jdg511/GAS/hardware/kicad/rev-a-capture-audit.md

# GAS Rev A Capture Audit

Generated by `python hardware/kicad/audit-rev-a-capture.py --output C:/Users/Jason/GAS-build/repo/hardware/kicad/rev-a-capture-audit.md`.

## Top-Level Hierarchy

- Hierarchical child sheets present: `6` / `6`
- Missing sheet files: none

## Symbol Population

| Sheet | Refs Found | Completion | Optional Refs Found |
| --- | ---: | ---: | ---: |
| io-board | 14/14 | 100.0% | 0 |
| tank-driver-recovery | 19/19 | 100.0% | 0 |
| ext-tank-routing | 12/12 | 100.0% | 0 |
| crossfade-feedback-wet | 8/8 | 100.0% | 0 |
| filter-clipper | 19/19 | 100.0% | 0 |
| power-backplane | 16/16 | 100.0% | 0 |

## Missing References By Sheet

### io-board

- Missing required refs: none

### tank-driver-recovery

- Missing required refs: none

### ext-tank-routing

- Missing required refs: none

### crossfade-feedback-wet

- Missing required refs: none

### filter-clipper

- Missing required refs: none

### power-backplane

- Missing required refs: none
- Optional refs still absent: `U601`

## Net Label Coverage

| Scope | Labels Found | Completion |
| --- | ---: | ---: |
| global | 5/5 | 100.0% |
| io-boundary | 8/8 | 100.0% |
| inter-board | 22/22 | 100.0% |
| control | 47/47 | 100.0% |

## Missing Net Labels

### global

- Missing labels: none

### io-boundary

- Missing labels: none

### inter-board

- Missing labels: none

### control

- Missing labels: none

## Notes

- This audit intentionally measures only what is visible in the checked-in schematic text: sheet files, symbol reference designators, and explicit labels.
- It does not claim analog correctness, ERC cleanliness, or footprint completeness.
- A placeholder child sheet will therefore score `0%` until real symbols and labels are entered.
