jdg511/GAS/hardware/kicad/datasheet_cache/g5v2.summary.md

# Omron G5V-2 (DPDT signal relay) — datasheet summary
Status: partially verified (contact ratings from text; coil table is a
graphic — needs-human-check at order time)
- Contacts: rated 0.5 A/125 VAC, 2 A/30 VDC; carry 2 A. Audio/logic signals
  here are mA-level: PASS with large margin.
- Coils used: DC5 (K201-K204, K401-K403; ~30-40 mA each assumed) and DC12
  (K301, fed from +15VA through R351 240R sized for a ~960R coil).
  ACTION AT ORDER: confirm coil resistance of the exact DC5/DC12 variants;
  if DC12 coil is 720R, R351 -> 150R.
- Pinout used: 1/16 coil; 4 COM1, 6 NC1, 8 NO1; 13 COM2, 11 NC2, 9 NO2
  (KiCad library symbol geometry). NC/NO polarity affects which panel
  position means 'inverted'/mode — bench-verify once, swap wires if flipped.
