jdg511/GAS/hardware/kicad/datasheet_cache/jst-vh.summary.md

# JST VH connector family — datasheet summary
Status: verified (rating block read visually, datasheet_cache/eVH_35d0fc229b.pdf p.1)
- 10 A (AWG#16) / 7 A (AWG#18), 250 V. Rails carry <=0.25 A/pin: <4%: PASS.
