jdg511/GAS/hardware/kicad/datasheet_cache/jst-xh.summary.md

# JST XH connector family — datasheet summary
Status: verified (rating block read visually, datasheet_cache/eXH_98b6fe789a.pdf p.1)
- 3 A AC/DC (AWG#22), 250 V, contact R 10 mOhm initial, wire 30-22 AWG.
- Worst path on XH here: +30 V DC input landing P500 ~0.36 A = 12%: PASS.
  Tank sends ~65 mA pk, audio signals lower: PASS.
