jdg511/GAS/hardware/kicad/datasheet_cache/opa1644.summary.md

# OPA1644 (SOIC-14 quad JFET audio op amp) — datasheet summary
Status: verified for supply range (cached PDF datasheet_cache/opa1644_652e77ac8c.pdf)
- Supply: +/-2.25 V to +/-18 V. +/-15 V used: PASS. JFET input, pA bias.
- KiCad symbol used: TL074 (identical industry quad pinout as above).
