jdg511/GAS/hardware/kicad/datasheet_cache/opa1656.summary.md

# OPA1656 (SOIC-8 dual audio op amp) — datasheet summary
Status: verified (pin table, ROC, cached PDF datasheet_cache/opa1656_eb3ddbf012.pdf)
## Key limits (datasheet text evidence)
- Supply: +/-2.25 V to +/-18 V (4.5-36 V). Design uses +/-15 V: PASS.
- Output current: 100 mA; short-circuit +/-100 mA.
- Iq ~3.9 mA/ch (~7.8 mA/package).
## Pin-level requirements (SOIC-8 dual)
1 OUT_A | 2 IN_A- | 3 IN_A+ | 4 V- | 5 IN_B+ | 6 IN_B- | 7 OUT_B | 8 V+
- V+/V- require local decoupling (100 nF class) per rail.
- CMOS inputs: pA bias; high-value bias resistors (2.2M) acceptable.
