jdg511/GAS/hardware/kicad/datasheet_cache/opa1679.summary.md

# OPA1679 (SOIC-14 quad audio op amp) — datasheet summary
Status: verified (supply range from cached PDF datasheet_cache/opa1679_e09979f1c7.pdf)
- Supply: +/-2.25 V to +/-18 V (4.5-36 V), ~2 mA/ch. +/-15 V used: PASS.
- Output-drive spec not text-extracted: loads in this design are >=10k or
  behind 100-220R isolators (<5 mA) — needs-human-check only for margins.
## Pins (standard quad): 1 OUT_A, 2 IN_A-, 3 IN_A+, 4 V+, 5 IN_B+, 6 IN_B-,
7 OUT_B, 8 OUT_C, 9 IN_C-, 10 IN_C+, 11 V-, 12 IN_D+, 13 IN_D-, 14 OUT_D.
