jdg511/GAS/hardware/kicad/datasheet_cache/r78e.summary.md

# RECOM R-78E5.0-0.5 — datasheet summary
Status: verified (text, datasheet_cache/R-78E-0.5_4908d77dcc.pdf)
- Input 7-28 VDC, output 5 V 0.5 A, 7805 pinout (1 Vin, 2 GND, 3 Vout).
- Fed from +15VRAW (review fix F1): inside range, PASS. Load worst-case
  ~210 mA (relay coils): 42% of rating, PASS.
- Externals: input cap C512 10u (added), output C507 47u + C508 100n: PASS.
