jdg511/GAS/hardware/kicad/review_outputs/filt-U401-U402.md

# Instance review: U401/U402 (OPA1679 x2, filter-clipper)
Datasheet summary: datasheet_cache/opa1679.summary.md

| Pin/Group | Net | Check | Result |
| --- | --- | --- | --- |
| U401 A/B | HPF buffers (47n + pot rheostat) | fc 33 Hz-3.4 kHz | pass (sim) |
| U401 C/D | drive 4.9x fixed | sim exact | pass |
| U402 A/B | LPF buffers (pot series + 10n) | fc 157 Hz-16 kHz | pass (sim) |
| U402 C/D | output buffers + 100R isolators |  | pass |
| power units | +/-15 V + 100n x4 + 22u x2 |  | pass |

## Required externals
Audio-path caps are film-footprint (1210 ECHU class): policy pass.

## Findings
None.

Evidence: extracted JSON (rebuild/review-extract-filter-clipper.json), raw .kicad_sch
spot-check, datasheet summary above, verified ngspice run. Confidence: high
unless noted.
