jdg511/GAS/hardware/kicad/review_outputs/tdr-Q101-Q104.md

# Instance review: Q101-Q104 (BD139-16/BD140-16, tank-driver-recovery)
Datasheet summary: datasheet_cache/bd139-bd140.summary.md

| Pin/Group | Net | Check | Result |
| --- | --- | --- | --- |
| B/C/E | base stoppers 68R; C to rails; 0.33R emitters to PRI_OUT | class-B in-loop | pass (sim) |
| bias reserve | D101/D102/D121/D122 DNP | spec-frozen reserve | pass |

## Required externals
Datasheet not cached: dissipation margin is schematic+sim consistency only.

## Findings
manual_review: verify SOA/hFE bin from ST datasheet before production.

Evidence: extracted JSON (rebuild/review-extract-tank-driver-recovery.json), raw .kicad_sch
spot-check, datasheet summary above, verified ngspice run. Confidence: high
unless noted.
