jdg511/GAS/hardware/kicad/review_outputs/tdr-U102-U104.md

# Instance review: U102-U104 (OPA1656 x3, tank-driver-recovery)
Datasheet summary: datasheet_cache/opa1656.summary.md

| Pin/Group | Net | Check | Result |
| --- | --- | --- | --- |
| U102 A/B | SEC sends, gain 2.2 into 800R tanks | sim: 1.04 Vpk out | pass |
| U103/U104 A/B | recovery, gain 34, 2.2M bias to AGND | CMOS pA bias: OK | pass |
| power units | +15VA/-15VA + 100n each | decoupling present | pass |

## Required externals
Recovery offset x34 -> ~17 mV DC downstream (bench note, see final report).

## Findings
None.

Evidence: extracted JSON (rebuild/review-extract-tank-driver-recovery.json), raw .kicad_sch
spot-check, datasheet summary above, verified ngspice run. Confidence: high
unless noted.
