jdg511/GAS/hardware/bom/rev-a-input-output-priced-bom.csv

Board | RefDes | Qty | Manufacturer | MPN | Description | UnitPrice | Currency | Supplier | ExtPrice | BuyURL | AssemblyScope | Notes
Input/Output | U1 | 1 | Texas Instruments | OPA1644AIDR | Quad JFET-input audio op amp | 4.65 | USD | DigiKey | 4.65 | https://www.digikey.com/en/products/detail/texas-instruments/OPA1644AIDR/2353575 | SMD | Balanced receiver and mono-routing utility; current DigiKey page still shows the part as not normally stocked
Input/Output | U2-U4 | 3 | Texas Instruments | OPA1656IDR | Dual audio op amp | 2.99 | USD | DigiKey | 8.97 | https://www.digikey.com/en/products/detail/texas-instruments/OPA1656IDR/10715414 | SMD | Wet/dry mix plus fully active balanced output stages
Input/Output | J1-J4 | 4 | Neutrik | NCJ6FI-S | Combo XLR female / 1/4 TRS chassis receptacle | 4.71 | USD | Mouser | 18.84 | https://www.mouser.com/ProductDetail/Neutrik/NCJ6FI-S?qs=2AuUxvzm3x9XIIQSbwRdvA%3D%3D | Panel-DNP | Panel part; usually excluded from SMT quote
Input/Output | P1 | 1 | JST Sales America Inc. | B3P-VH-B | 3-position 3.96mm through-hole header | 0.23 | USD | DigiKey | 0.23 | https://www.digikey.com/en/products/detail/jst-sales-america-inc/B3P-VH-B/9924220 | TH | Board power input
Input/Output | P2-P4,P6 (+ P5 family placeholder) | 5 | JST Sales America Inc. | B3B-XH-A | 2.50mm JST XH-family header pricing placeholder | 0.15 | USD | DigiKey | 0.75 | https://www.digikey.com/en/products/detail/jst-sales-america-inc/B3B-XH-A/1651046 | TH | Priced as the common XH-family baseline only; `P5` is actually a larger 6-wire wet/dry landing and must be finalized as the matching higher-position XH-family part during the real PCB release
