jdg511/GAS/hardware/bom/rev-a-panel-and-mechanical-reference-bom.csv

Category | Subsystem | Qty | Manufacturer | MPN | Description | UnitPrice | Currency | Supplier | ExtPrice | BuyURL | Notes
Combo Jack | External I/O | 4 | Neutrik | NCJ6FI-S | Combo XLR female / 1/4 TRS chassis receptacle, solder cup | 4.71 | USD | Mouser | 18.84 | https://www.mouser.com/ProductDetail/Neutrik/NCJ6FI-S?qs=2AuUxvzm3x9XIIQSbwRdvA%3D%3D | Current reference combo-jack family for the fixed XLR/TRS requirement
Combo Jack Alt | External I/O | 4 | Neutrik | NCJ6FA-H | Combo XLR female / 1/4 TRS chassis receptacle, horizontal PCB mount | 0 | USD | Neutrik | 0 | https://www.neutrik.com/en/product/ncj6fa-h | Alternative if the enclosure and PCB benefit from direct combo-jack PCB mounting
DC Jack | Chassis Power | 1 | Same Sky | PJ-005A | Panel-mount DC barrel jack, 5.5 mm OD / 2.1 mm ID, center positive | 3.07 | USD | DigiKey | 3.07 | https://www.digikey.com/en/products/detail/same-sky-formerly-cui-devices/PJ-005A/165838 | Matches the Triad WSU240-0750 wall-adapter barrel size; same mounting hole as PJ-005B
Round Endcap Blank | Mechanical | 1 | Online Metals | AL-6061-PLATE-10IN-0125 | Reference 6061 aluminum plate blank for circular service endcap, 10 in x 0.125 in | 0 | USD | OnlineMetals | 0 | https://www.onlinemetals.com/en/buy/aluminum/0-125-aluminum-plate-6061-t6/pid/21631 | Size changed 9 in -> 10 in with diameter decision; price and exact SKU need requote at 10 in
Reinforcement Plate | Mechanical | 1 | Online Metals | AL-5052-PLATE-7IN-0090 | Reference aluminum reinforcement plate for jack bar and control support | 8.65 | USD | OnlineMetals | 8.65 | https://www.onlinemetals.com/en/buy/aluminum/0-09-aluminum-sheet-5052-h32/pid/11292 | Reference raw stock for the internal jack bar or local stiffener
Standoff Kit | Mechanical | 1 | Keystone | 2203 | Aluminum hex standoff assortment reference, 4-40 thread | 6.20 | USD | DigiKey | 6.20 | https://www.digikey.com/en/products/detail/keystone-electronics/2203/316133 | Reference internal rail or board-mount hardware
