jdg511/GAS/hardware/bom/rev-a-power-backplane-priced-bom.csv

Board | RefDes | Qty | Manufacturer | MPN | Description | UnitPrice | Currency | Supplier | ExtPrice | BuyURL | AssemblyScope | Notes
Power Backplane | J500 | 1 | Same Sky | PJ-005A | Panel-mount DC barrel jack, 5.5 mm OD / 2.1 mm ID, center positive | 3.07 | USD | DigiKey | 3.07 | https://www.digikey.com/en/products/detail/same-sky-formerly-cui-devices/PJ-005A/165838 | Panel-DNP | Service-endcap DC input jack; matches Triad WSU240-0750 2.1mm plug; same mounting hole/hardware as prior PJ-005B
Power Backplane | EXT-PSU | 1 | Triad Magnetics | WSU240-0750 | External wall adapter, +24VDC 750mA 18W regulated SMPS, UL 62368-1, 5.5x2.1mm center-positive plug | 12.43 | USD | DigiKey | 12.43 | https://www.digikey.com/en/products/detail/triad-magnetics/WSU240-0750/3094933 | External | Selected 2026-07-04; supersedes Jameco DDU300050E9340 candidate; alternates: Tri-Mag L6R20-240, Triad WSU240-1000
Power Backplane | PS500 | 1 | Mornsun | URA2415YMD-10WR3 | Isolated DC-DC module, 9-36V in (24V nominal), +/-15V dual at 10W out | 9.27 | USD | DigiKey | 9.27 | https://www.digikey.com/en/products/detail/mornsun-america-llc/URA2415YMD-10WR3/13160913 | SMD-or-module | Primary +/-15V generation
Power Backplane | PS501 | 1 | RECOM | R-78E5.0-0.5 | Switching regulator module, +5V/500mA out | 3.37 | USD | DigiKey | 3.37 | https://www.digikey.com/en/products/detail/recom-power/R-78E5-0-0-5/2834904 | SMD-or-module | +5VAUX generation
Power Backplane | P501-P505 | 5 | JST Sales America Inc. | B3P-VH-B | 3-position 3.96mm through-hole header | 0.23 | USD | DigiKey | 1.15 | https://www.digikey.com/en/products/detail/jst-sales-america-inc/B3P-VH-B/9924220 | TH | Split-rail board power outputs
Power Backplane | P506 | 1 | JST Sales America Inc. | B4P-VH-B | 4-position 3.96mm through-hole header | 0.29 | USD | DigiKey | 0.29 | https://www.digikey.com/en/products/detail/jst-sales-america-inc/B4P-VH-B/9924221 | TH | Ext-routing board power output including +5VAUX
