jdg511/GAS/hardware/kicad/release-exports/top-level-hierarchy-test-erc.txt

ERC report (2026-06-28T13:55:43, Encoding UTF8)
Report includes: Errors, Warnings, Exclusions

***** Sheet /

***** Sheet /input-output/

***** Sheet /tank-driver-recovery/

***** Sheet /ext-tank-routing/

***** Sheet /crossfade-feedback-wet/

***** Sheet /filter-clipper/

***** Sheet /power-backplane/

 ** ERC messages: 0  Errors 0  Warnings 0

 ** Ignored checks:
    - Global label only appears once in the schematic
    - Four connection points are joined together
    - SPICE model issue
    - Assigned footprint doesn't match footprint filters
