jdg511/GAS/hardware/kicad/release-exports/rev-a-release/pdf/ext-tank-routing.pdf

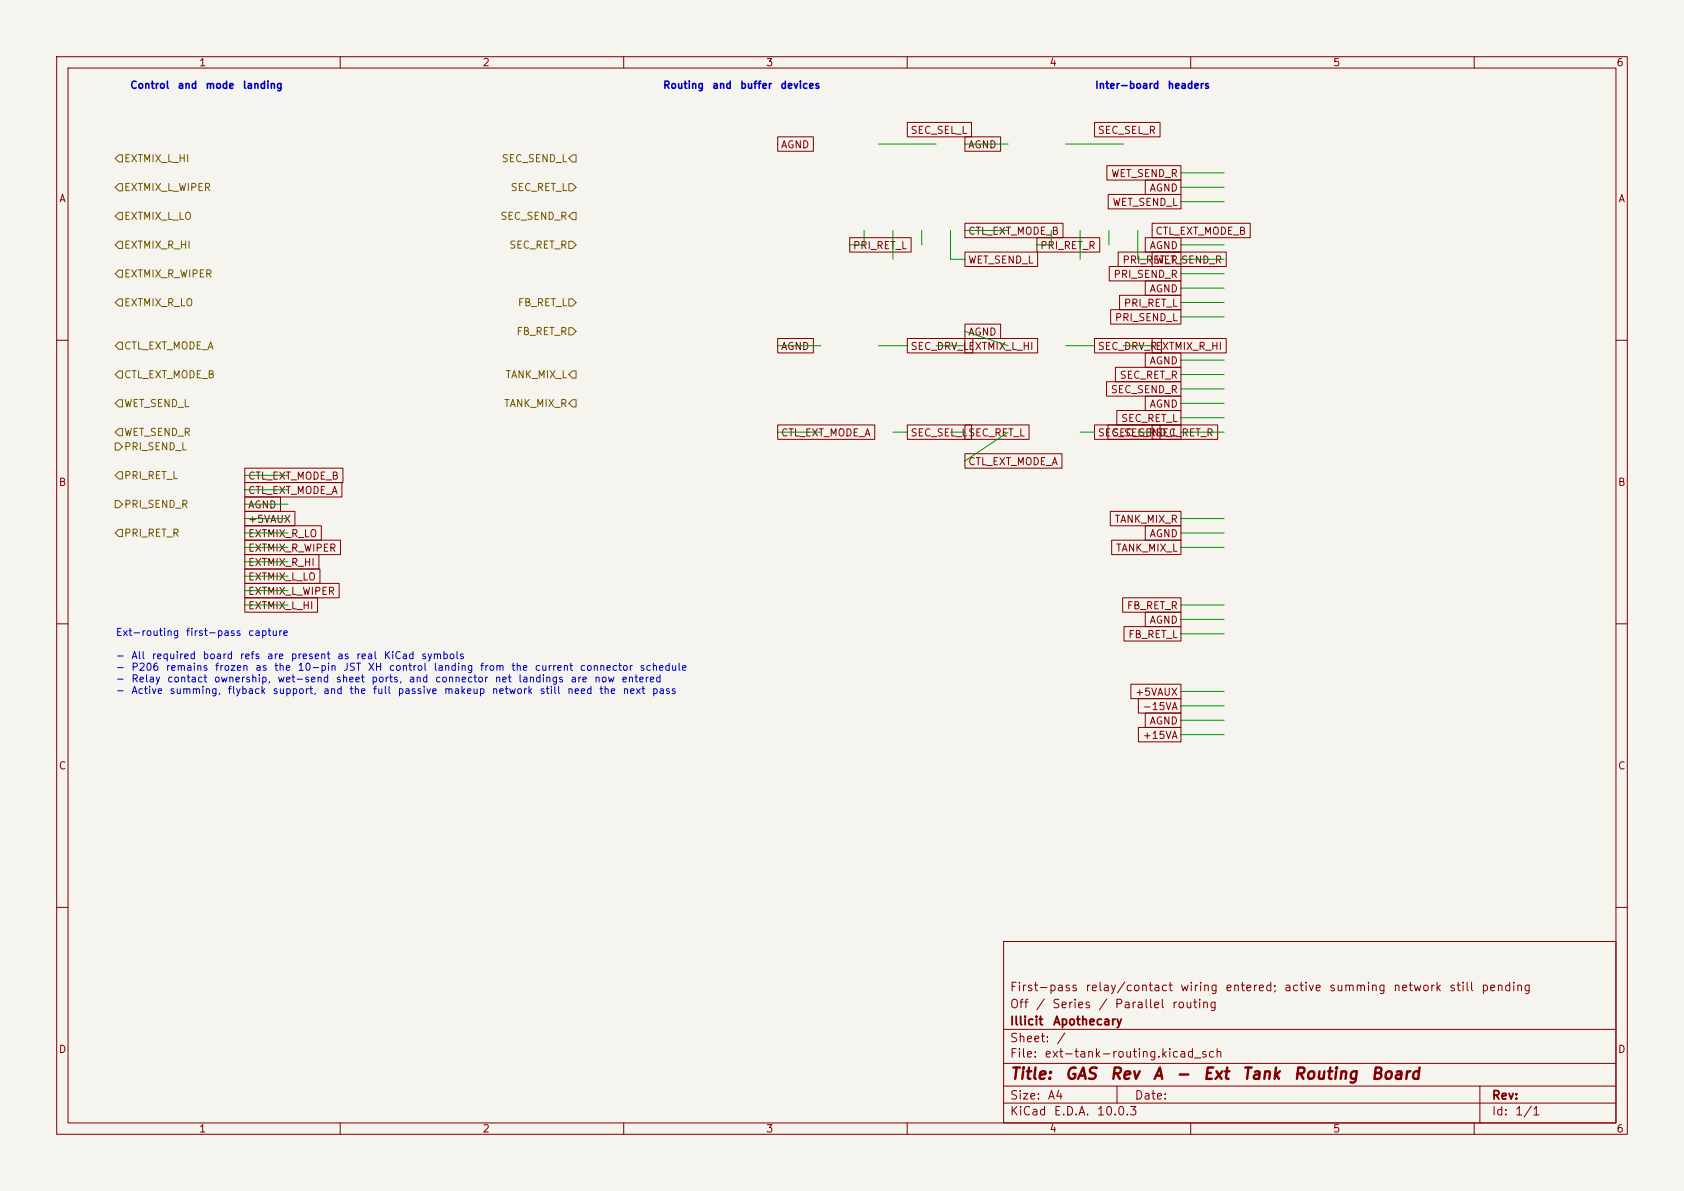
[picture p14: page 1]

Routing and buffer devices Ext-routing first-pass capture - All required board refs are present as real KiCad symbols - P206 remains frozen as the 10-pin JST XH control landing from the current connector schedule - Relay contact ownership, wet-send sheet ports, and connector net landings are now entered - Active summing, flyback support, and the full passive makeup network still need the next pass

First-pass relay/contact wiring entered; active summing network still pending
Off / Series / Parallel routing
Illicit Apothecary
Sheet: /
File: ext-tank-routing.kicad_sch
Title: GAS Rev A - Ext Tank Routing Board

Size: A4 | Rev:
KiCad E.D.A. 10.0.3 | Id: 1/1
