jdg511/GAS/hardware/kicad/release-exports/rev-a-release/pdf/filter-clipper.pdf

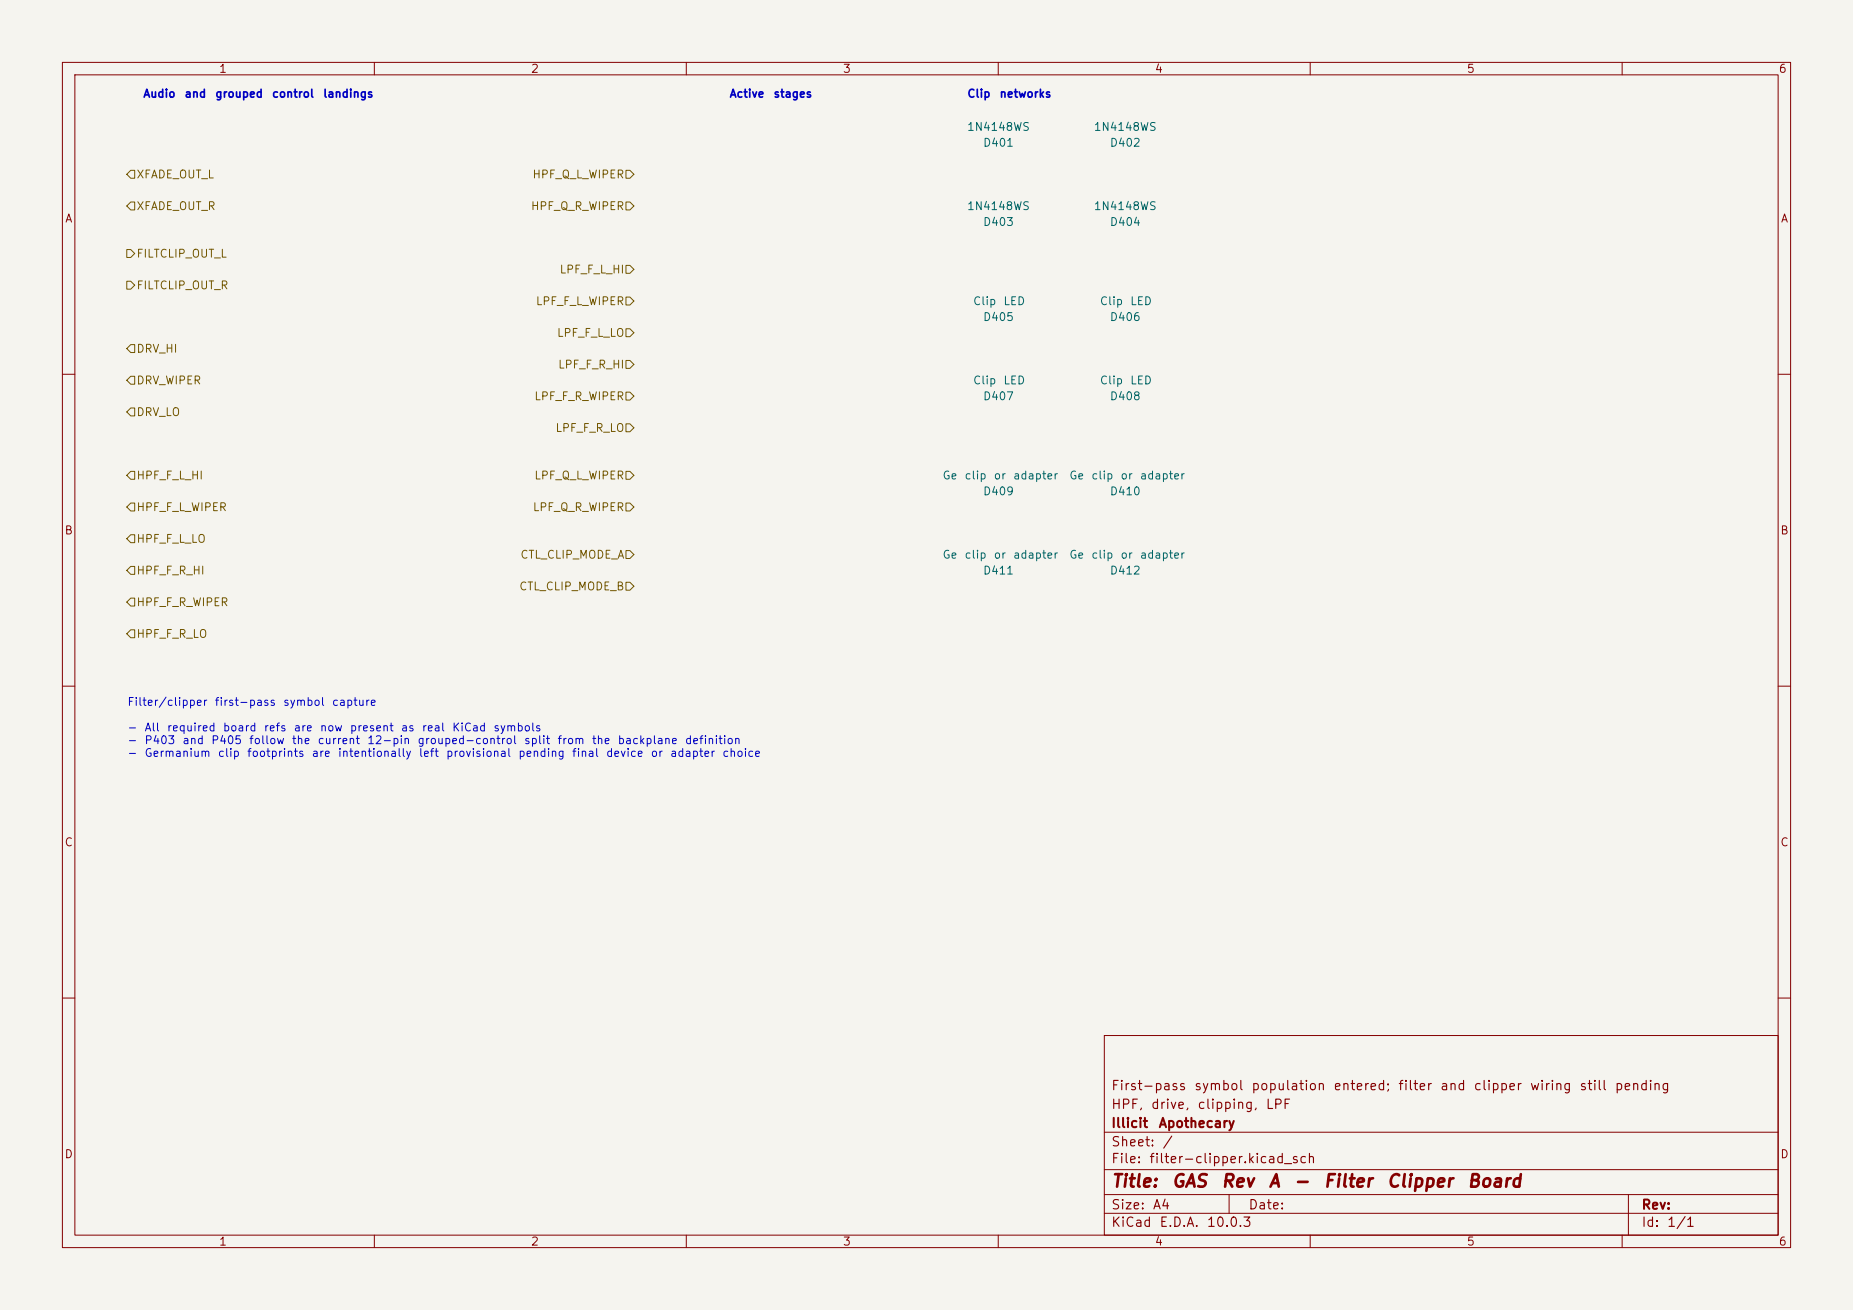
[picture p15: page 1]

First-pass symbol population entered; filter and clipper wiring still pending
HPF, drive, clipping, LPF
Illicit Apothecary
Sheet: /
File: filter-clipper.kicad_sch
Title: GAS Rev A - Filter Clipper Board

Size: A4 | Rev:
KiCad E.D.A. 10.0.3 | Id: 1/1
