jdg511/GAS/hardware/kicad/release-exports/rev-a-release/pdf/io-board.pdf

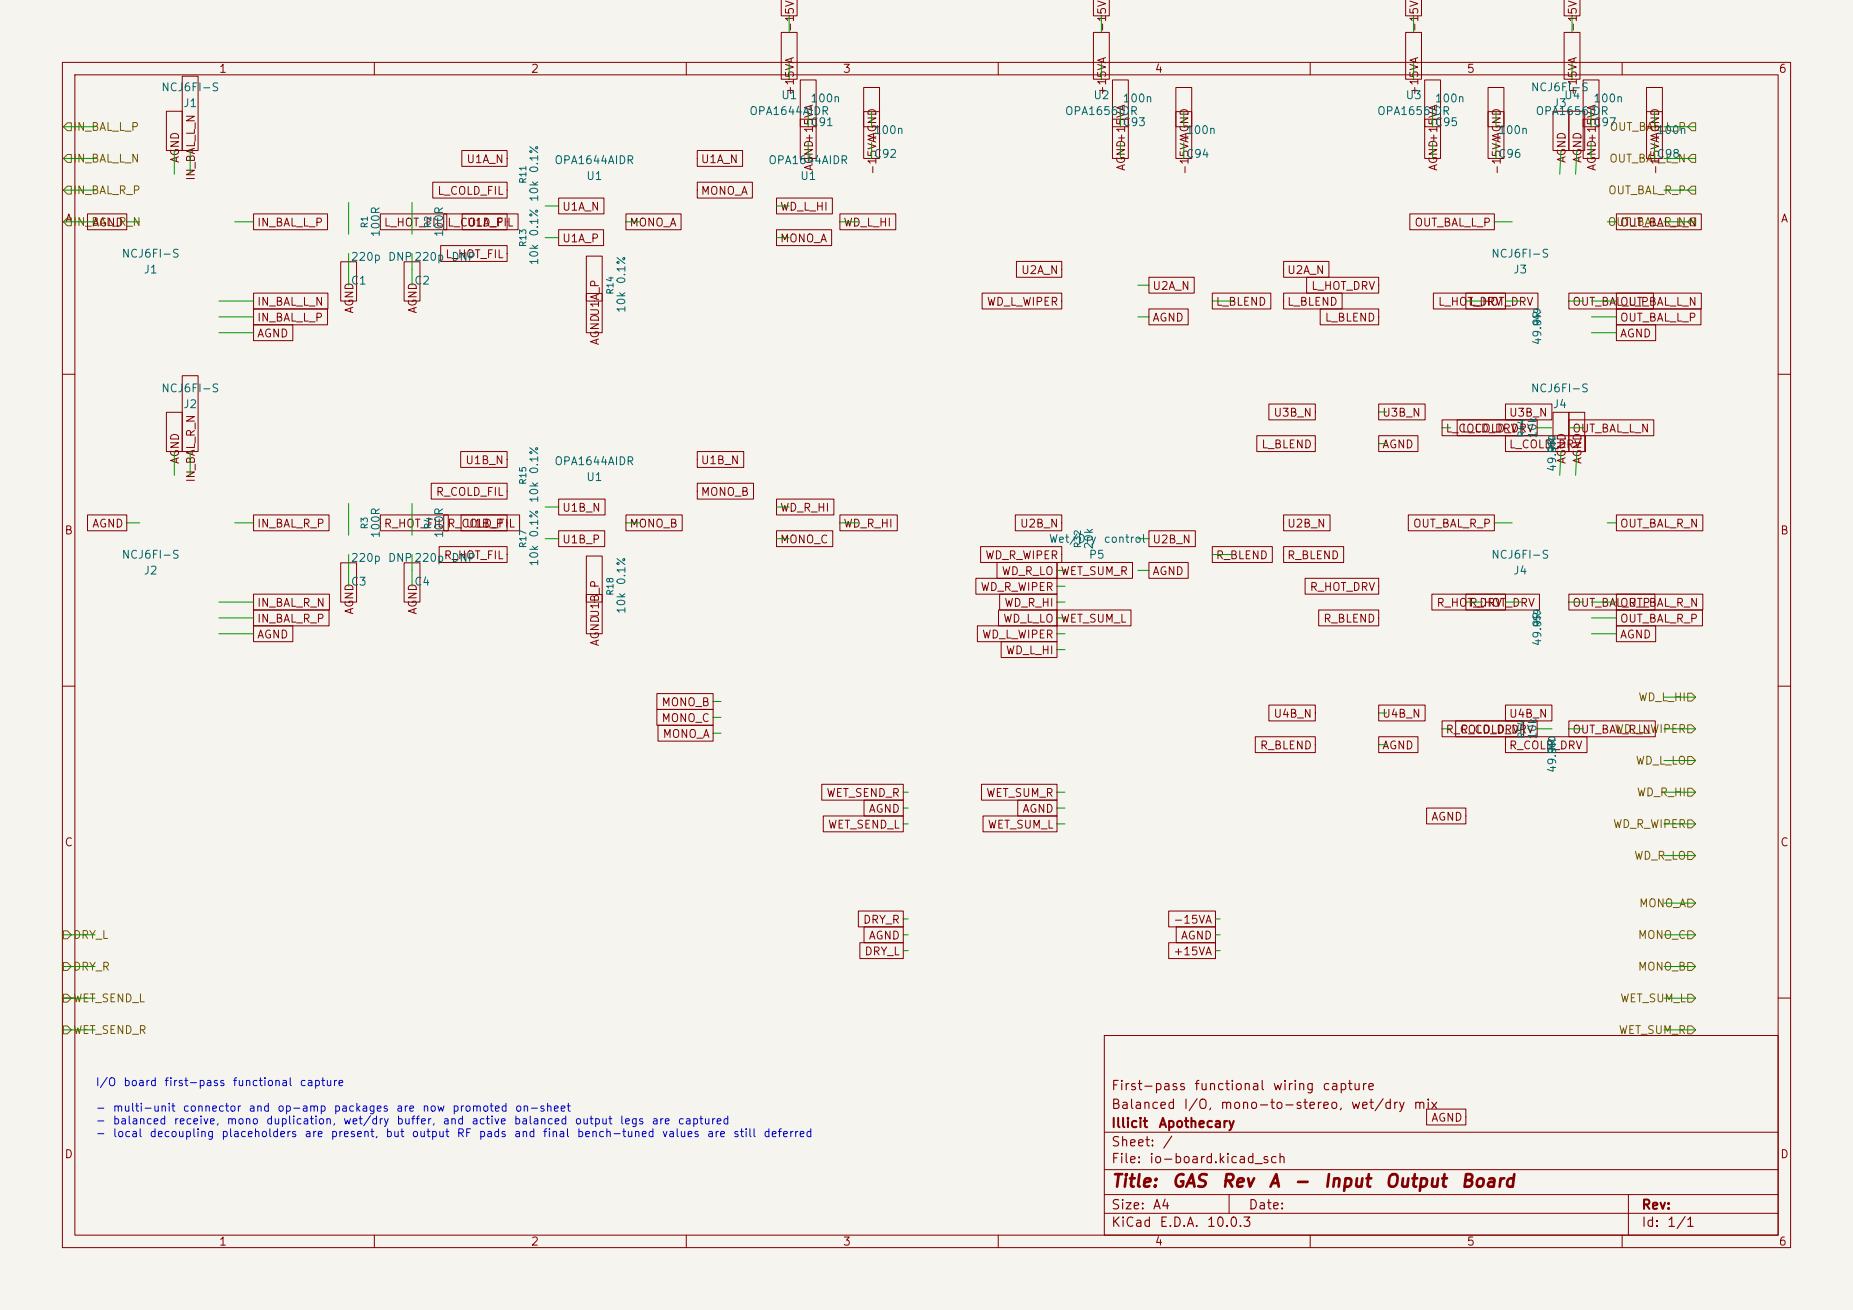
[picture p16: page 1]

I/O board first-pass functional capture - multi-unit connector and op-amp packages are now promoted on-sheet - balanced receive, mono duplication, wet/dry buffer, and active balanced output legs are captured - local decoupling placeholders are present, but output RF pads and final bench-tuned values are still deferred

First-pass functional wiring capture
Balanced I/O, mono-to-stereo, wet/dry mix
Illicit Apothecary
Sheet: /
File: io-board.kicad_sch
Title: GAS Rev A - Input Output Board

Size: A4 | Rev:
KiCad E.D.A. 10.0.3 | Id: 1/1
