jdg511/GAS/hardware/kicad/release-exports/rev-a-release/pdf/power-backplane.pdf

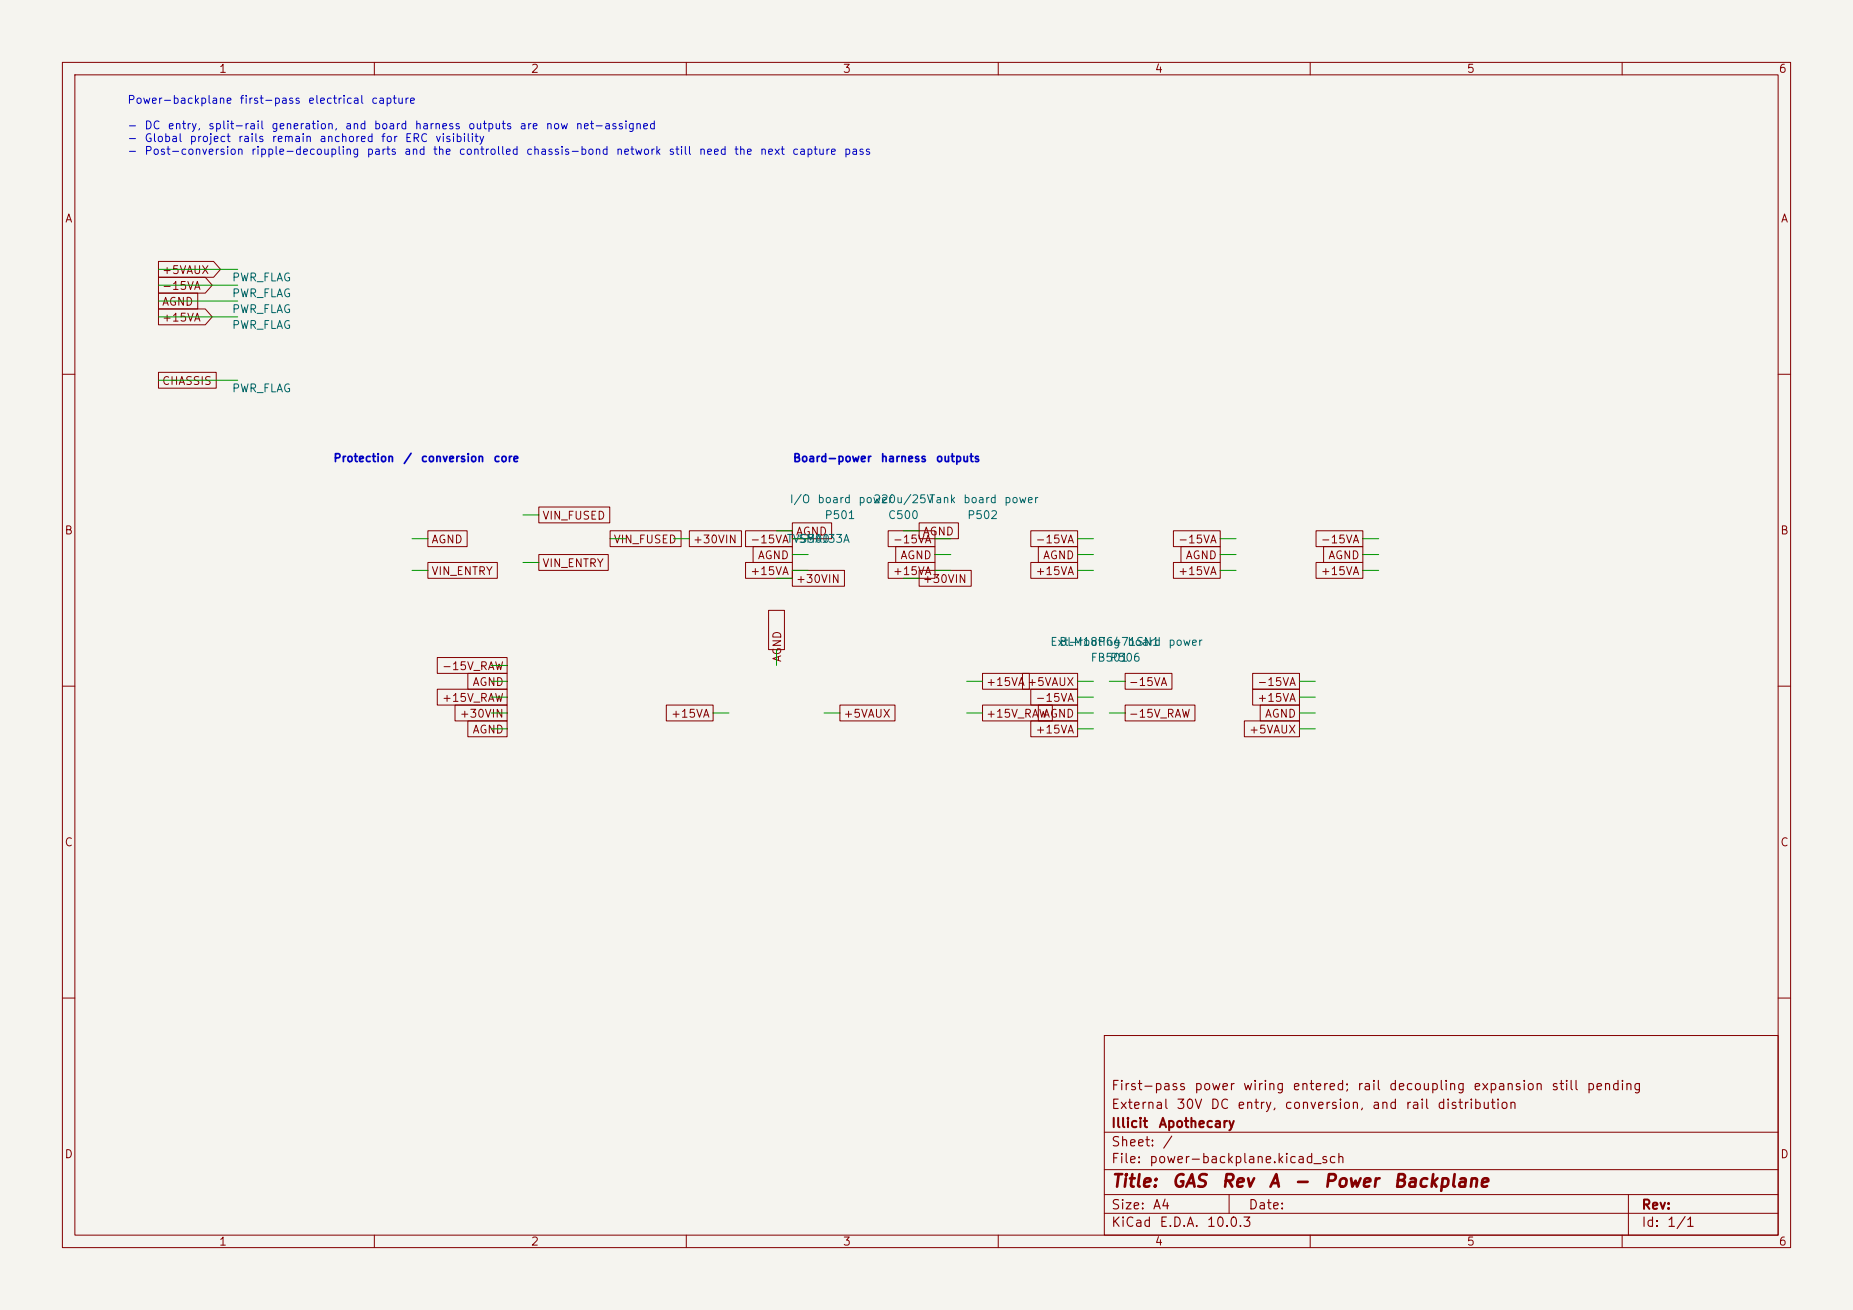
[picture p17: page 1]

AGND -15VA +15V_RAW +15VA +15VA +5VAUX Protection / conversion core Power-backplane first-pass electrical capture - DC entry, split-rail generation, and board harness outputs are now net-assigned - Global project rails remain anchored for ERC visibility - Post-conversion ripple-decoupling parts and the controlled chassis-bond network still need the next capture pass Board-power harness outputs PWR_FLAG

Ext-routing board power P502

First-pass power wiring entered; rail decoupling expansion still pending
External 30V DC entry, conversion, and rail distribution
Illicit Apothecary
Sheet: /
File: power-backplane.kicad_sch
Title: GAS Rev A - Power Backplane

Size: A4 | Rev:
KiCad E.D.A. 10.0.3 | Id: 1/1
