jdg511/GAS/hardware/kicad/release-exports/rev-a-release/pdf/tank-driver-recovery.pdf

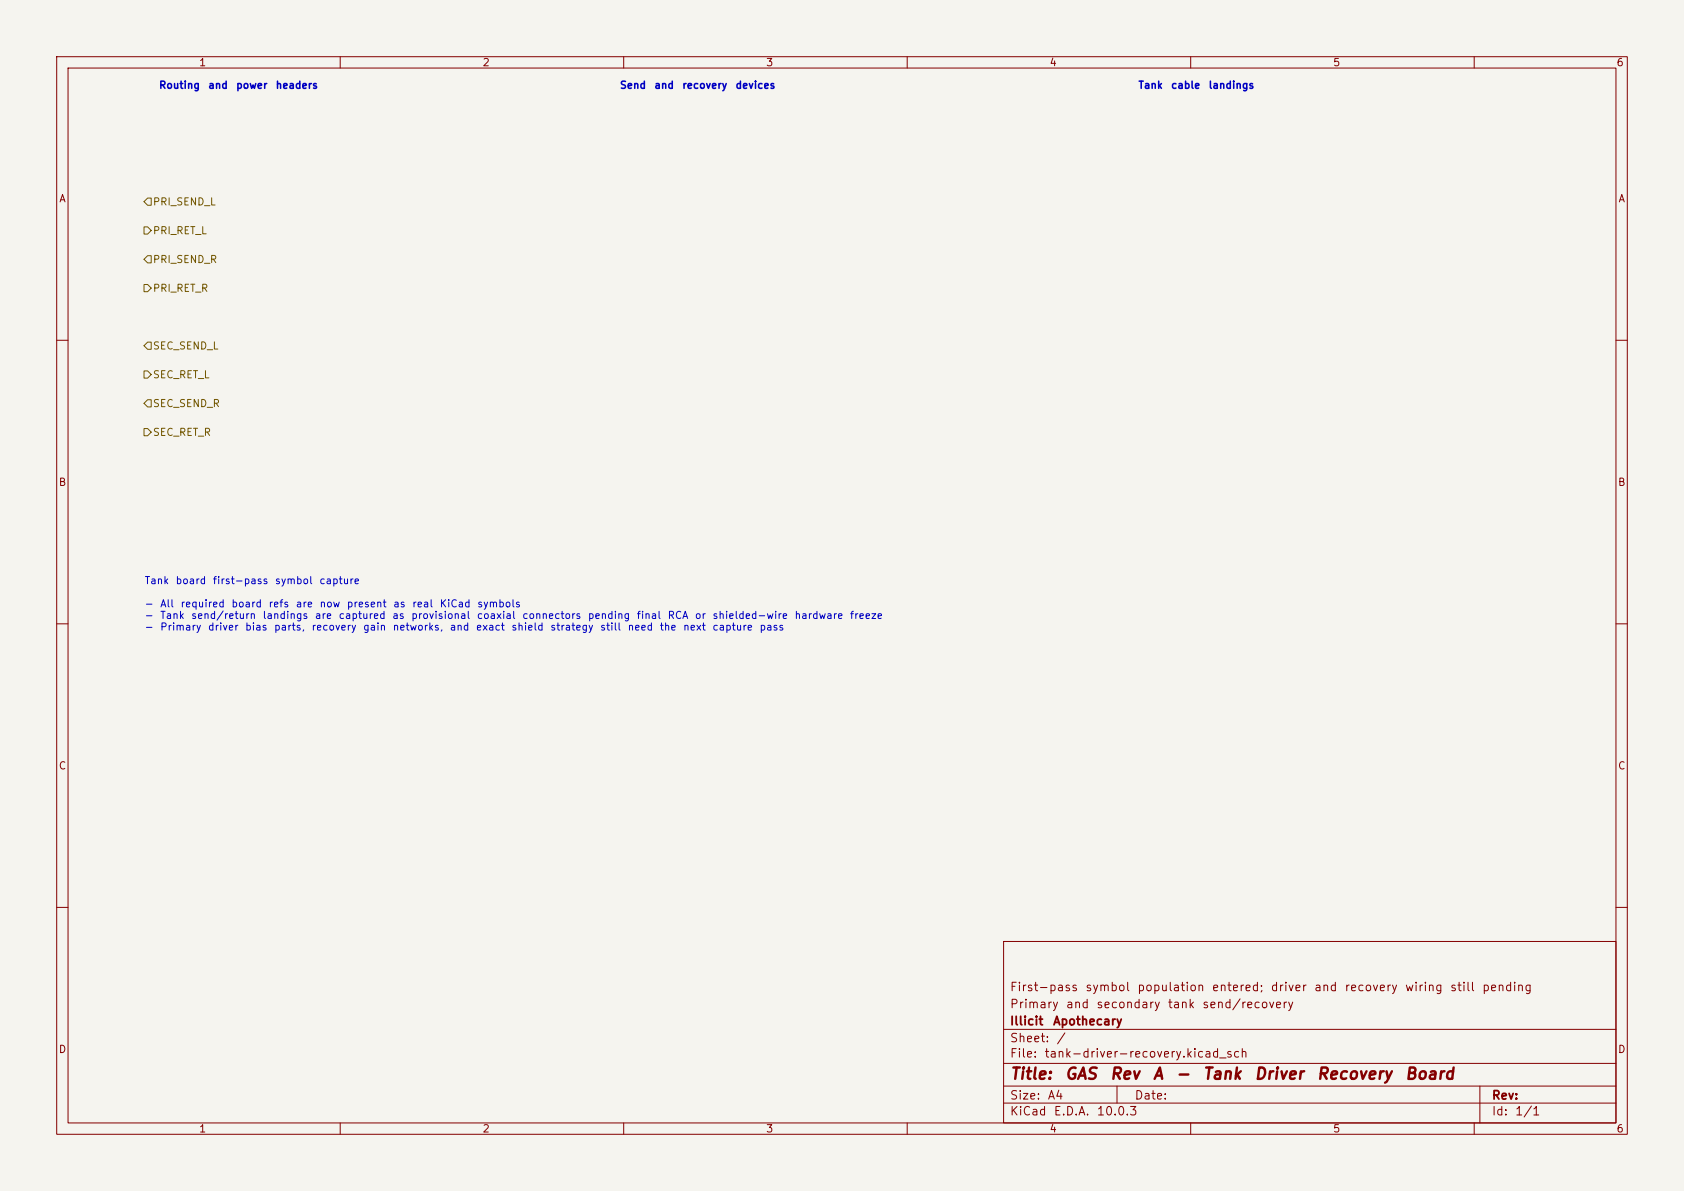
[picture p18: page 1]

Routing and power headers

Tank board first-pass symbol capture - All required board refs are now present as real KiCad symbols - Tank send/return landings are captured as provisional coaxial connectors pending final RCA or shielded-wire hardware freeze - Primary driver bias parts, recovery gain networks, and exact shield strategy still need the next capture pass

First-pass symbol population entered; driver and recovery wiring still pending
Primary and secondary tank send/recovery
Illicit Apothecary
Sheet: /
File: tank-driver-recovery.kicad_sch
Title: GAS Rev A - Tank Driver Recovery Board

Size: A4 | Rev:
KiCad E.D.A. 10.0.3 | Id: 1/1
