jdg511/GAS/hardware/kicad/release-exports/rev-a-release/pdf/top-level.pdf

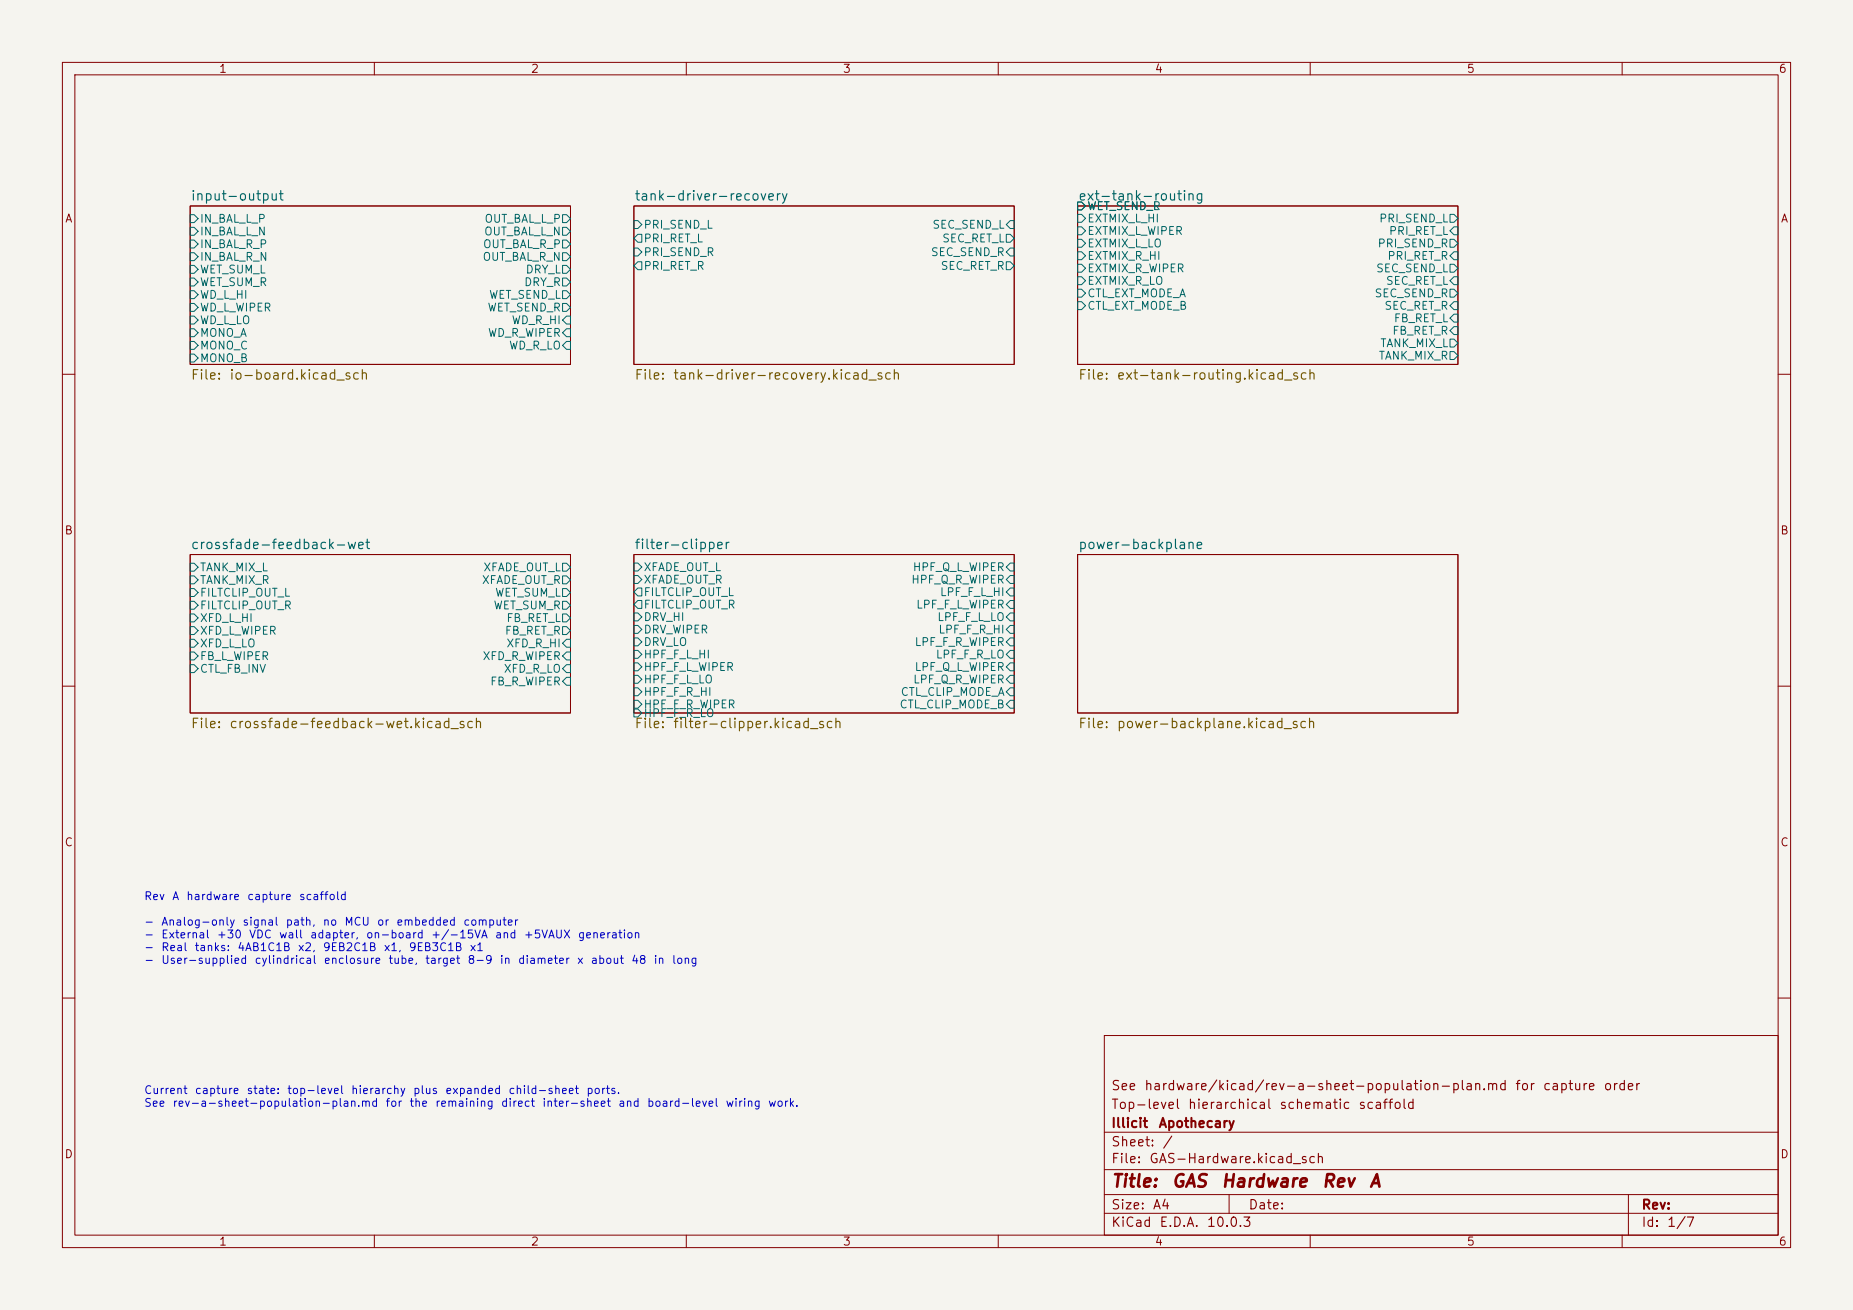
[picture p19: page 1]

File: ext-tank-routing.kicad_sch

File: crossfade-feedback-wet.kicad_sch

Rev A hardware capture scaffold - Analog-only signal path, no MCU or embedded computer - External +30 VDC wall adapter, on-board +/-15VA and +5VAUX generation - Real tanks: 4AB1C1B x2, 9EB2C1B x1, 9EB3C1B x1 - User-supplied cylindrical enclosure tube, target 8-9 in diameter x about 48 in long Current capture state: top-level hierarchy plus expanded child-sheet ports. See rev-a-sheet-population-plan.md for the remaining direct inter-sheet and board-level wiring work.

See hardware/kicad/rev-a-sheet-population-plan.md for capture order
Top-level hierarchical schematic scaffold
Illicit Apothecary
Sheet: /
File: GAS-Hardware.kicad_sch
Title: GAS Hardware Rev A

Size: A4 | Rev:
KiCad E.D.A. 10.0.3 | Id: 1/7

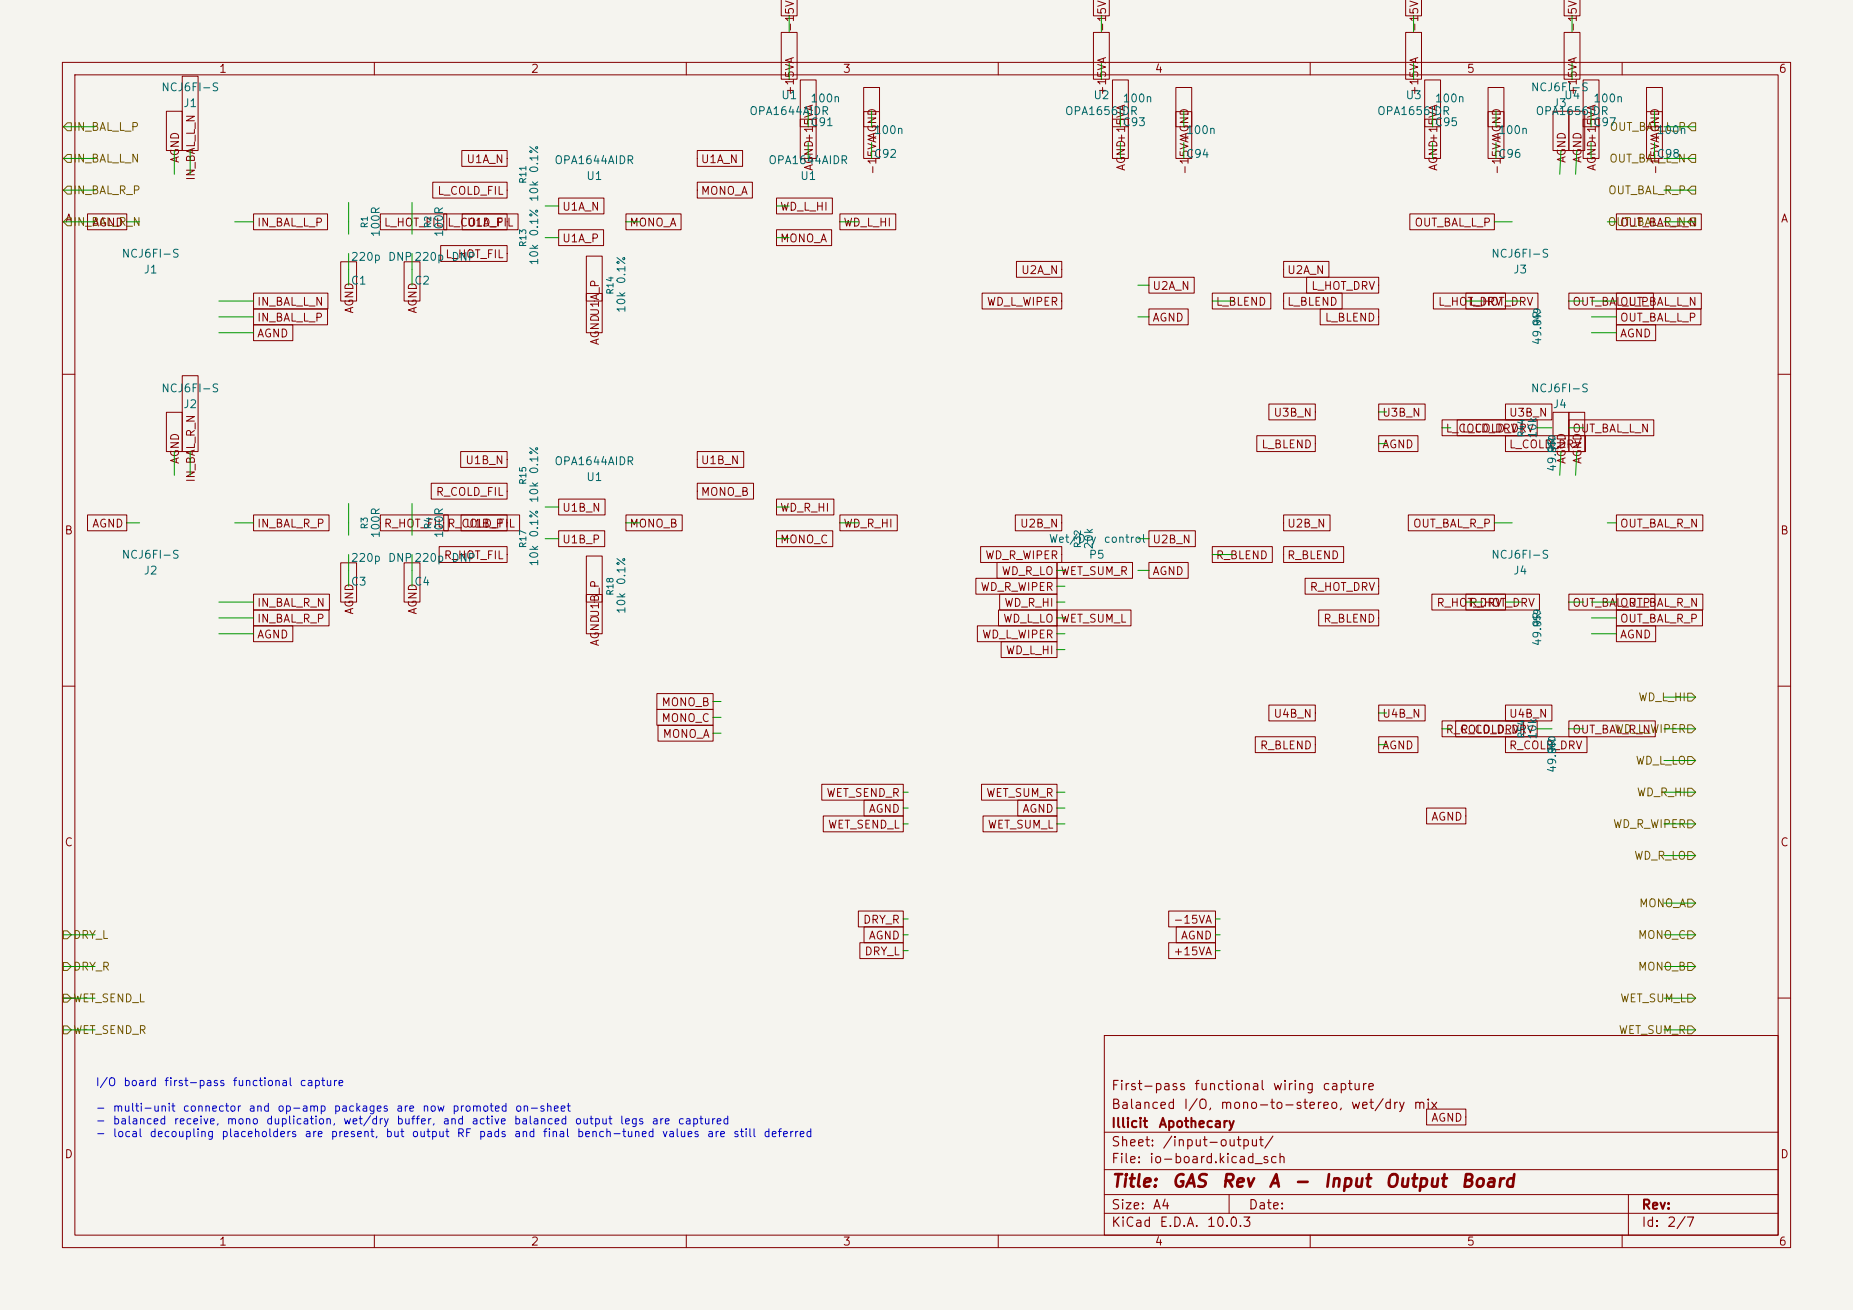
[picture p20: page 2]

I/O board first-pass functional capture - multi-unit connector and op-amp packages are now promoted on-sheet - balanced receive, mono duplication, wet/dry buffer, and active balanced output legs are captured - local decoupling placeholders are present, but output RF pads and final bench-tuned values are still deferred

First-pass functional wiring capture
Balanced I/O, mono-to-stereo, wet/dry mix
Illicit Apothecary
Sheet: /input-output/
File: io-board.kicad_sch
Title: GAS Rev A - Input Output Board

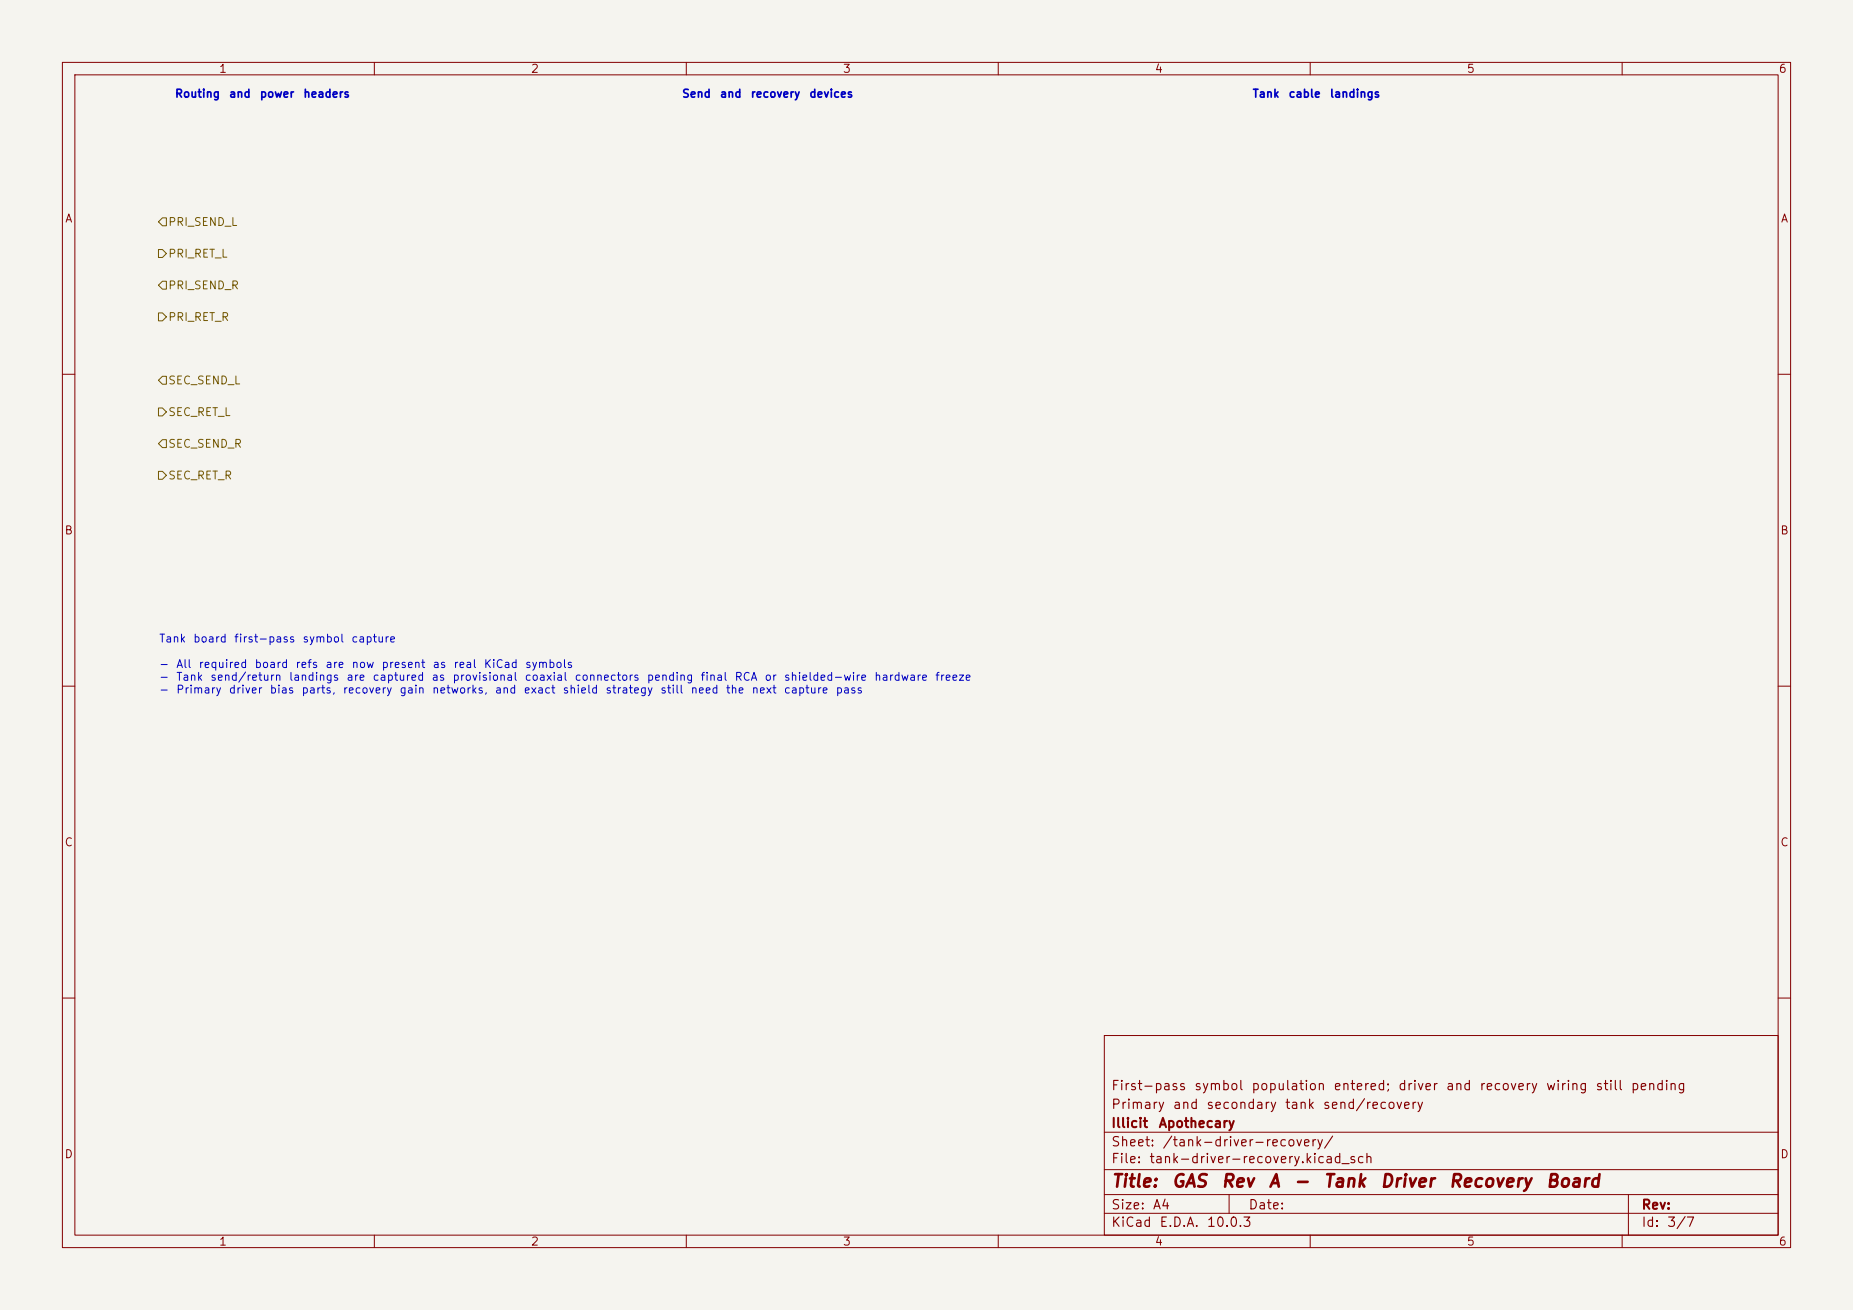
[picture p21: page 3]

Routing and power headers

Tank board first-pass symbol capture - All required board refs are now present as real KiCad symbols - Tank send/return landings are captured as provisional coaxial connectors pending final RCA or shielded-wire hardware freeze - Primary driver bias parts, recovery gain networks, and exact shield strategy still need the next capture pass

First-pass symbol population entered; driver and recovery wiring still pending
Primary and secondary tank send/recovery
Illicit Apothecary
Sheet: /tank-driver-recovery/
File: tank-driver-recovery.kicad_sch
Title: GAS Rev A - Tank Driver Recovery Board

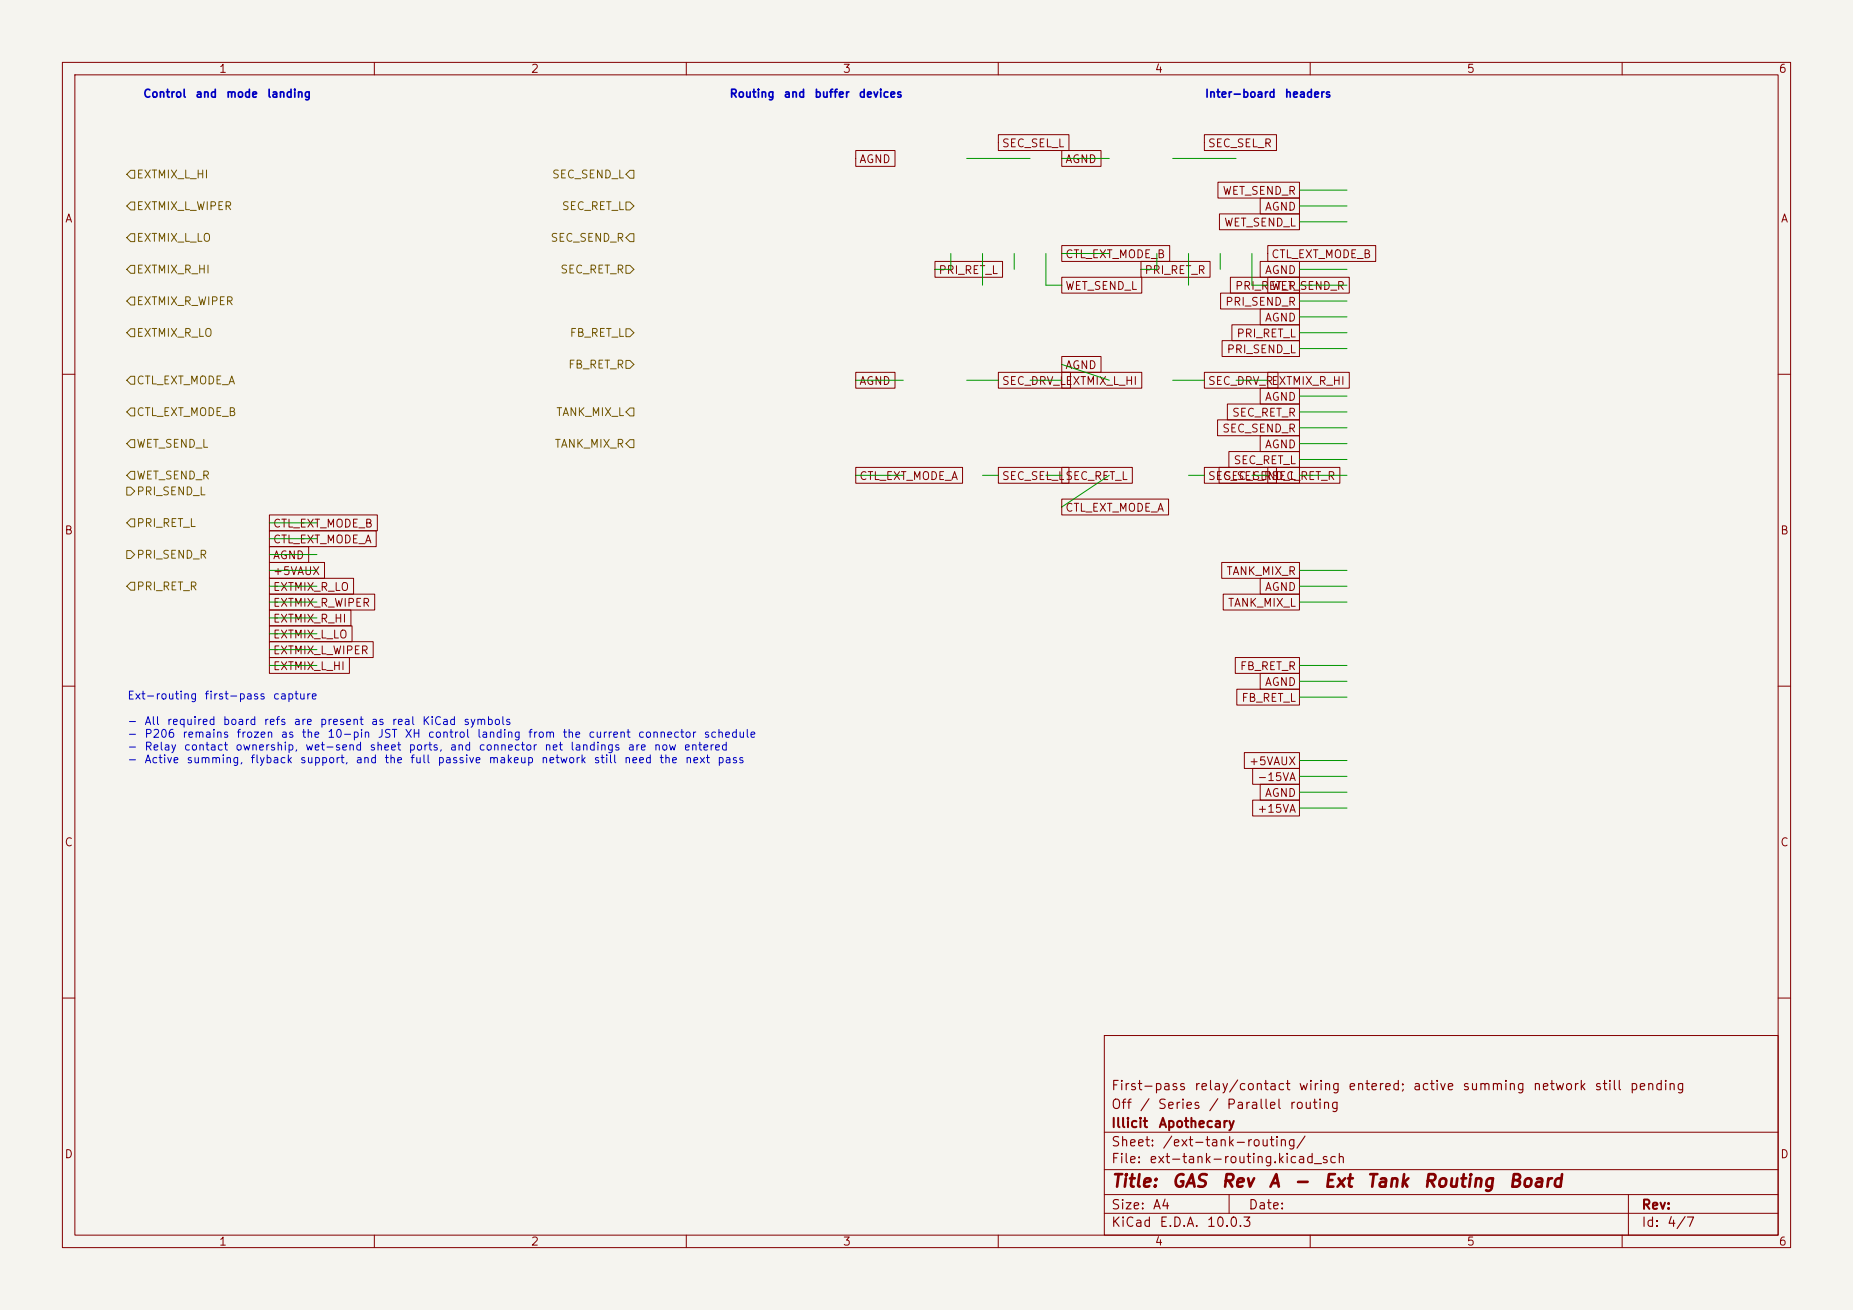
[picture p22: page 4]

Routing and buffer devices Ext-routing first-pass capture - All required board refs are present as real KiCad symbols - P206 remains frozen as the 10-pin JST XH control landing from the current connector schedule - Relay contact ownership, wet-send sheet ports, and connector net landings are now entered - Active summing, flyback support, and the full passive makeup network still need the next pass

First-pass relay/contact wiring entered; active summing network still pending
Off / Series / Parallel routing
Illicit Apothecary
Sheet: /ext-tank-routing/
File: ext-tank-routing.kicad_sch
Title: GAS Rev A - Ext Tank Routing Board

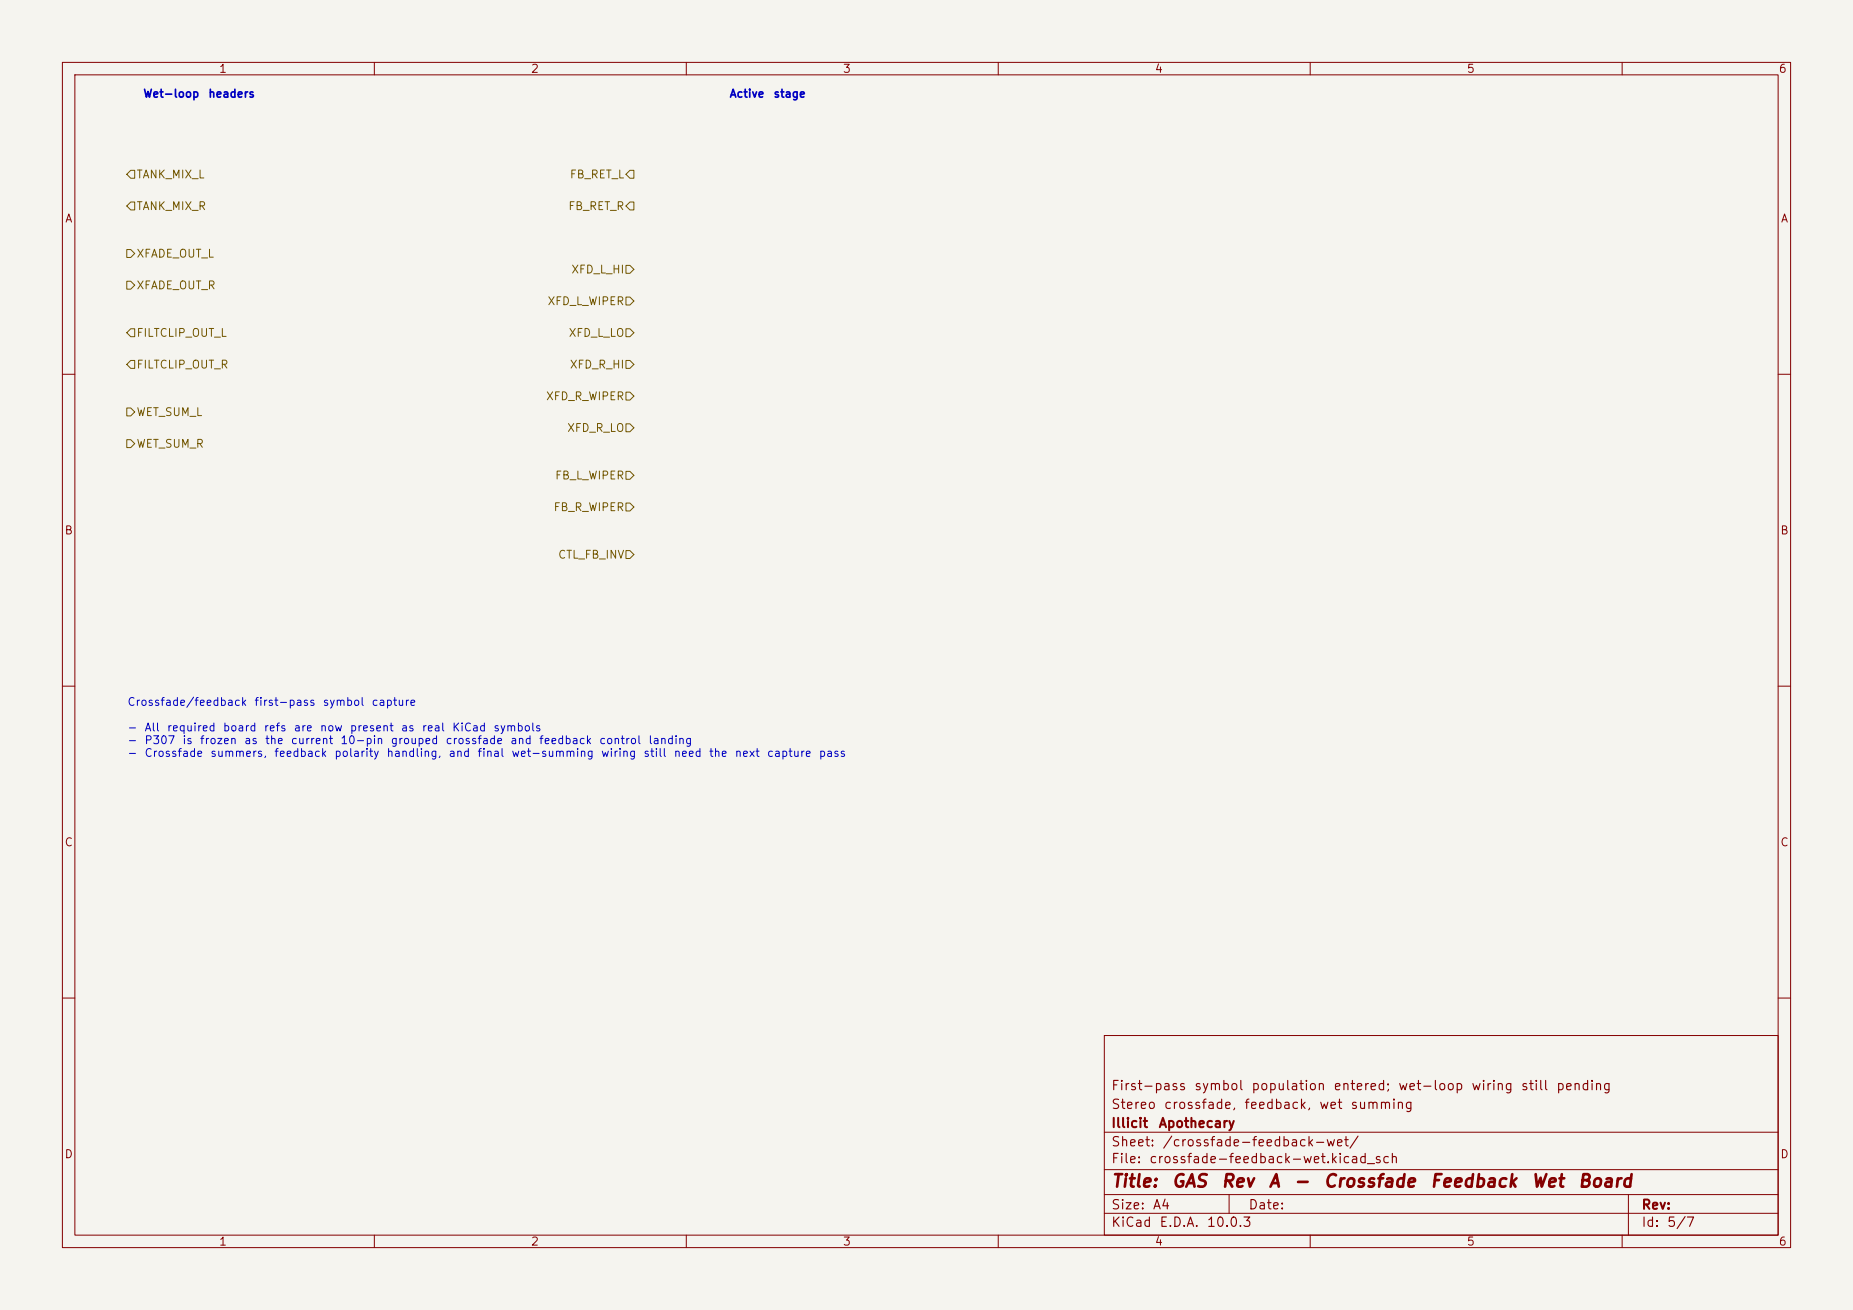
[picture p23: page 5]

Crossfade/feedback first-pass symbol capture - All required board refs are now present as real KiCad symbols - P307 is frozen as the current 10-pin grouped crossfade and feedback control landing - Crossfade summers, feedback polarity handling, and final wet-summing wiring still need the next capture pass

First-pass symbol population entered; wet-loop wiring still pending
Stereo crossfade, feedback, wet summing
Illicit Apothecary
Sheet: /crossfade-feedback-wet/
File: crossfade-feedback-wet.kicad_sch
Title: GAS Rev A - Crossfade Feedback Wet Board

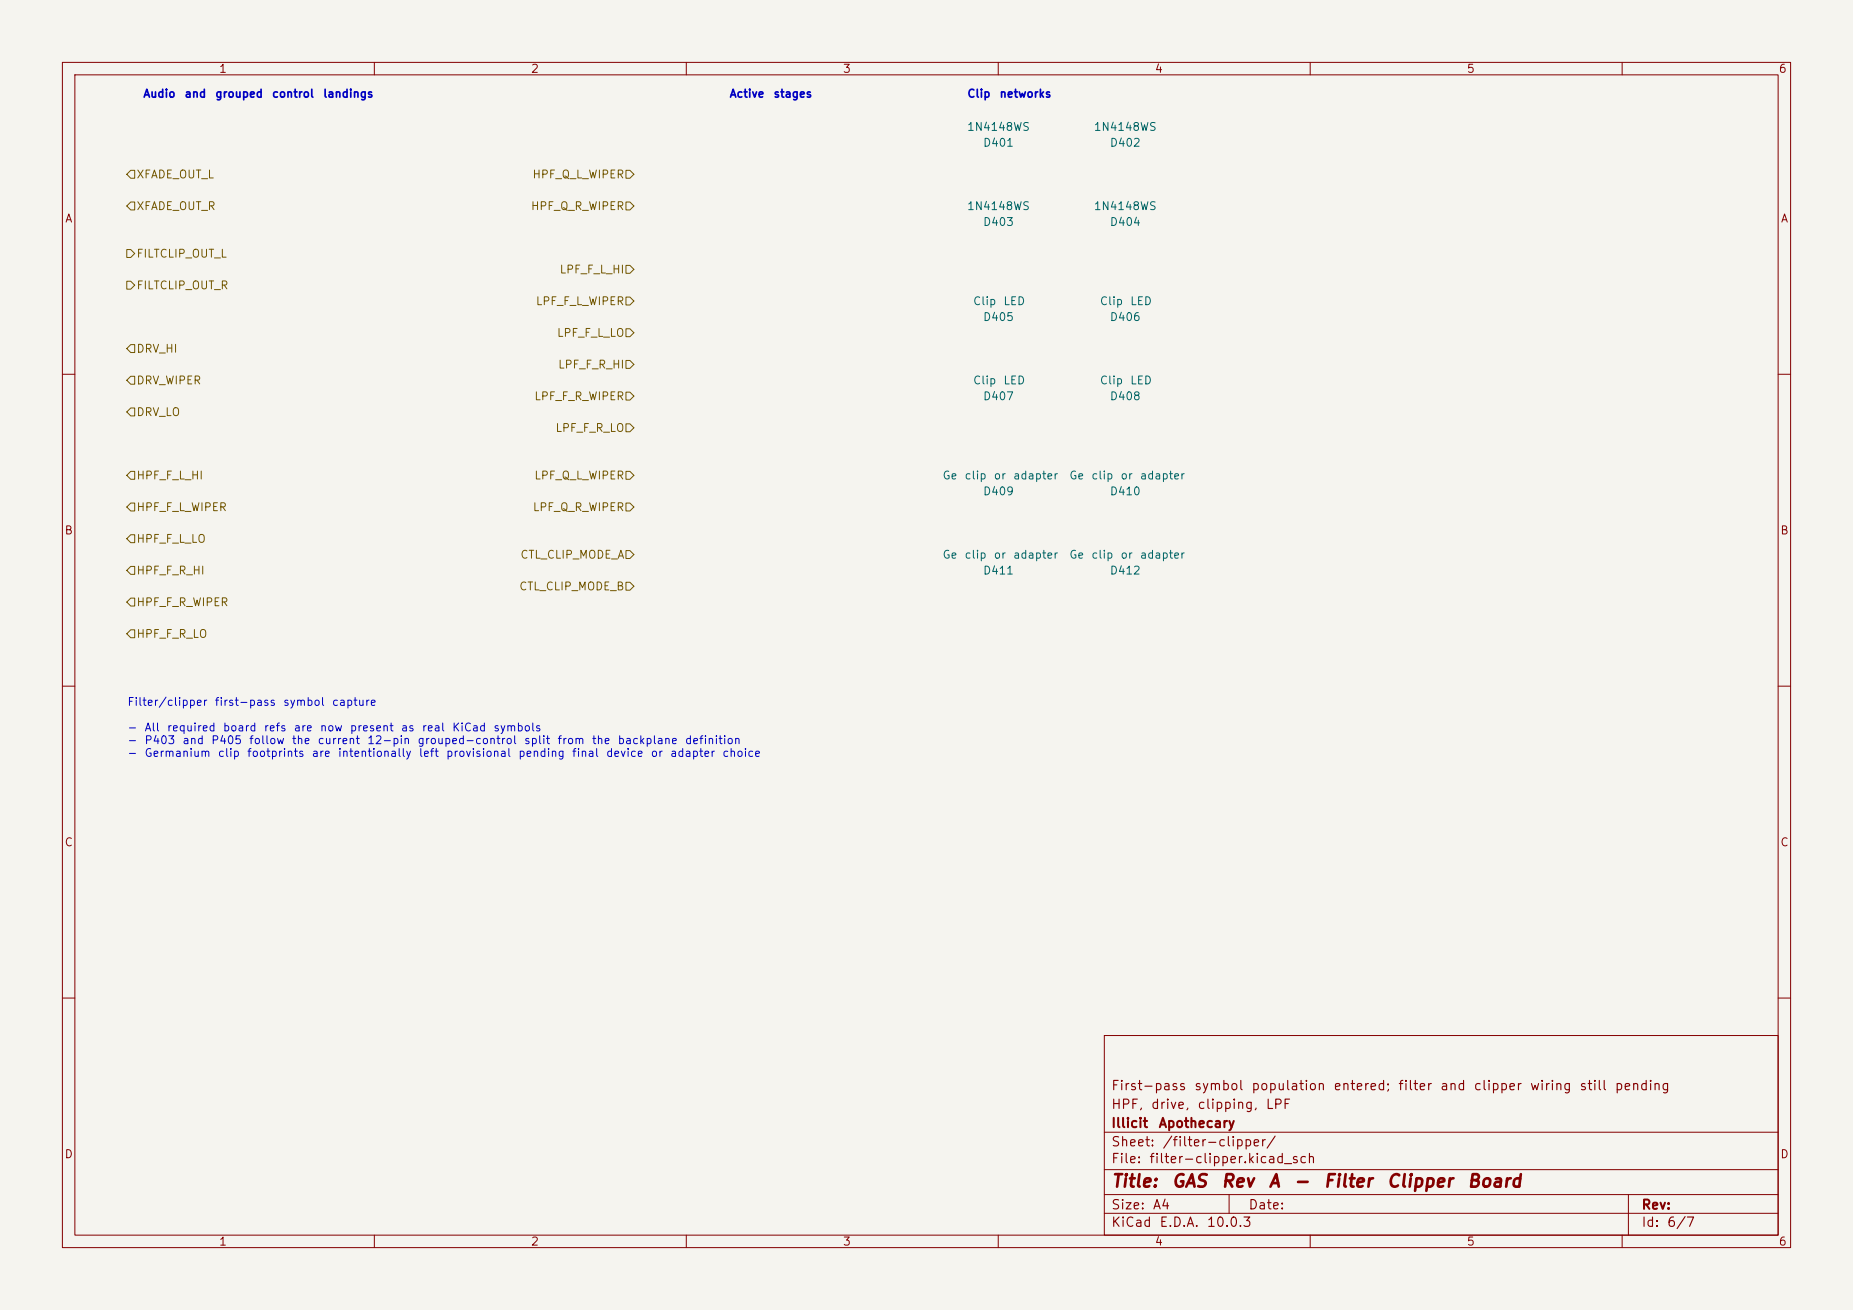
[picture p24: page 6]

First-pass symbol population entered; filter and clipper wiring still pending
HPF, drive, clipping, LPF
Illicit Apothecary
Sheet: /filter-clipper/
File: filter-clipper.kicad_sch
Title: GAS Rev A - Filter Clipper Board

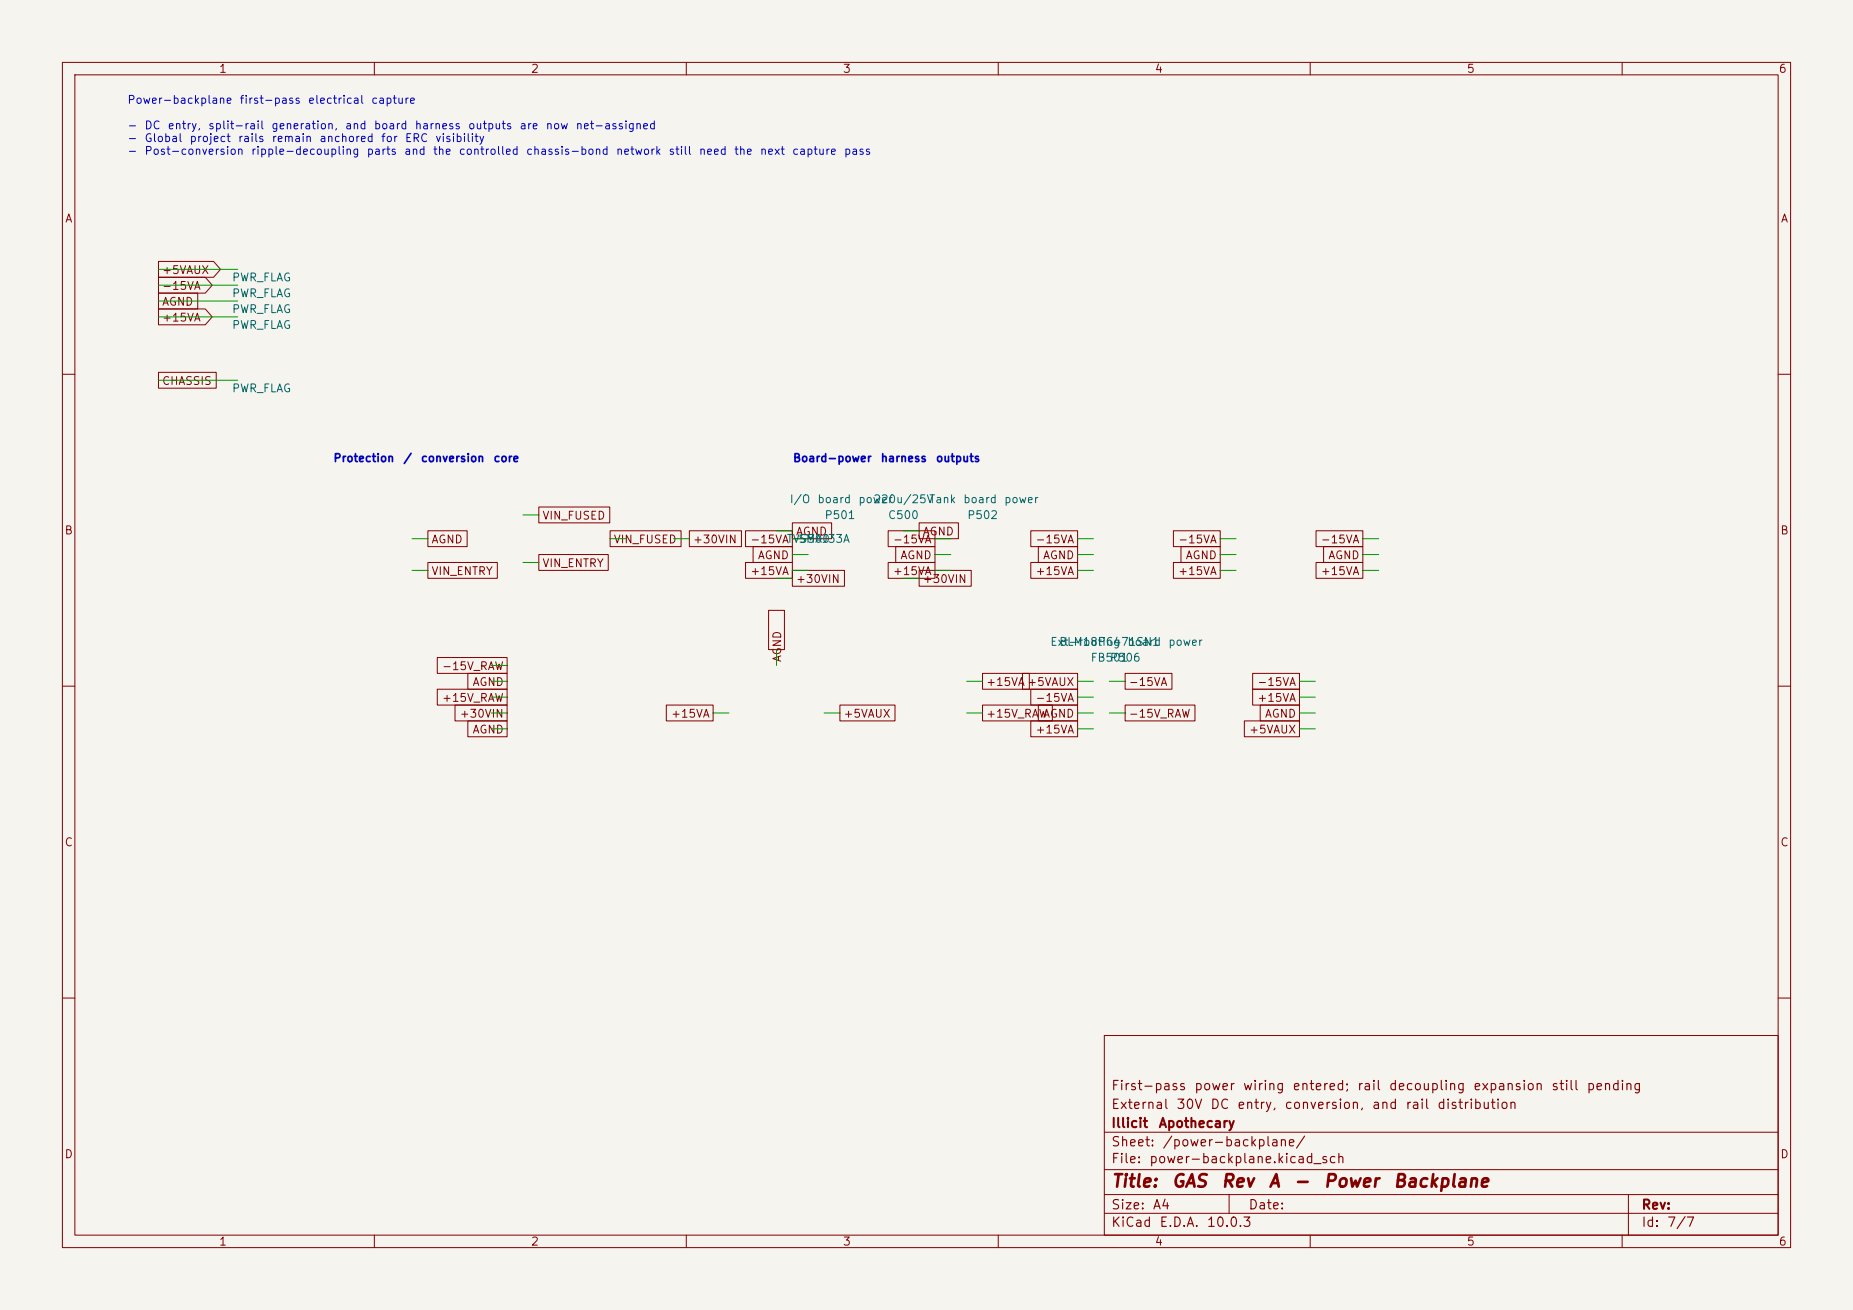
[picture p25: page 7]

AGND -15VA +15V_RAW +15VA +15VA +5VAUX Protection / conversion core Power-backplane first-pass electrical capture - DC entry, split-rail generation, and board harness outputs are now net-assigned - Global project rails remain anchored for ERC visibility - Post-conversion ripple-decoupling parts and the controlled chassis-bond network still need the next capture pass Board-power harness outputs PWR_FLAG

Ext-routing board power P502

First-pass power wiring entered; rail decoupling expansion still pending
External 30V DC entry, conversion, and rail distribution
Illicit Apothecary
Sheet: /power-backplane/
File: power-backplane.kicad_sch
Title: GAS Rev A - Power Backplane
